joscthomas/jctsh/tos/Repo-Purposes.md

# Repo Purposes

**Author:** Joseph C Thomas (JCT), via Claude
**Purpose:** What each repo under `Projects/` is actually *for* — not the mechanical
description (that's `Projects/README.md`'s one-liner, and each repo's own `README.md`),
but the real benefit it serves and who it serves. Prompted by a sermon note (jctsh
`tos/kanban-board.md` CARD-0320): "It's not just about the system, it is about the
results, the benefits for people."
**Version:** 1.3
**Version description:** Added `Rethinking-Scripture-Bible-Study`'s section — a fourth
repo under `Projects/`, created after this doc's first three entries. From v1.3 onward,
writing this section is a standard step of `New-Repo-Setup-Protocol.md` (step 9) for any
future repo, not something done after the fact.

---

**Template each entry follows:** Primary beneficiary → Origin → Core value/satisfaction
→ Secondary beneficiaries (if any) → Emergent/secondary purpose (if one exists — not
forced) → Open question / where this is heading (if genuinely unresolved).

## jctsh

- **Primary beneficiary:** Joseph.
- **Origin:** a decade of general tech interest (a SmartThings hub, basic household
  sensors), accelerating sharply in the last year into hands-on ESP32 firmware, circuit
  design, and 3D printing — a lifelong pull toward building tools and tinkering with
  electronics, from a career that started in programming before moving into
  project/program management.
- **Core value / satisfaction:** the puzzle itself — multi-dimensional, spanning
  hardware, firmware, and now AI-assisted development — and the specific pleasure of
  problem-solving through to something that actually works. A distinct, especially
  strong thread: Joseph hikes several times a week, and building gadgets to bring on
  those hikes (`hiking-monitor`, `air-quality-monitor`, `hike-izer`) is not incidental
  to the rest of the hobby — it's one of its clearest expressions.
- **Secondary beneficiary:** Robin — benefits from specific features, not all of it,
  and is generally supportive of the time Joseph spends on it.
- **Emergent/secondary purpose:** writing ESP32 firmware became the on-ramp to
  understanding AI-assisted development, initially by accident and now deliberately —
  using AI/Claude Code to build out a personal "operating system" (echoing jctsh's own
  `tos/` naming) is now an explicit, exciting direction in its own right, not just a
  side effect of the hobby.
- **Note on "critical":** not everything here is load-bearing (the garage door
  automation isn't essential infrastructure), but several things have become
  genuinely, daily-enjoyed conveniences regardless — the line between "hobby project"
  and "thing we actually rely on and like using" isn't as clean as it might sound.

## LogSeq

- **Primary beneficiary:** Joseph.
- **Origin:** a long-standing want to keep track of notes for a variety of purposes,
  after trying different note-taking tools over the years. LogSeq's specific model —
  daily journals, tagging, plain markdown files — is what's actually worked.
- **Core value / satisfaction:** central to Joseph's life, and reflected heavily in
  what gets captured here, is an ongoing pursuit — as a follower of Jesus, developing a
  real relationship with God and learning to love God and people, worked at for a long
  time, not a phase or a project with an end state. Notes along these lines (sermon
  notes, devotionals, scripture reflection) resonate with that quest and are a natural,
  central use of the tool.
- **Also tracked here, not secondary in importance, just distinct:** other things that
  matter to Joseph — ideas, ordinary life notes, now music — alongside the above, not
  subordinate to it.
- **Open question, not yet resolved:** how to actually *leverage* what accumulates here
  — not just capture and file it away, but do something more with it. Working with this
  repo and its tools (a Claude Code session operating directly in it, as this session
  has) may turn out to be part of how that gets figured out.

## PB-Blog

*Blog by Pastor Ben Walls, Sr. (pastorbenwalls.com). "Rethinking Scripture" is a separate repo (the new Bible study content, CARD-0317) — not this blog's title; corrected 2026-09-20 after conflating the two.*

- **Beneficiaries:** blog readers, Pastor Ben, and Joseph himself — serving these
  constituents while also learning through the editor role.
- **Origin:** ~20 years serving as editor for Pastor Ben's devotional blog — learned
  WordPress and the craft of editing/publishing itself first.
- **Core value / satisfaction:** started as learning the craft of editing and
  publishing; has grown into learning and using an increasingly augmented toolset
  (Grammarly, and now Claude-assisted editing/formatting automation) — a genuine
  learning bonus, echoing jctsh's AI-learning thread but in a different register: here
  it's a welcome side benefit of the editorial work, not (yet) a deliberate central
  direction the way it's become in jctsh.
- **Real risk this repo addresses — not platform risk, key-person risk:** the concern
  isn't WordPress disappearing, it's the risk of losing the person (Joseph) who's been
  driving this for so many years. A clean, technology-independent representation of the
  material — a real source of truth, per PB-Blog's own `kanban-board.md` CARD-0003 —
  would outlast any one person's continued involvement, not just any one platform.
- **Emergent purpose:** persisting Pastor Ben's legacy — a genuine service to him, with
  benefit extending to his family. Possible futures this could enable: a searchable
  archive, or Pastor Ben or his family compiling a book from the material. Who else
  might find it valuable isn't known, and that's fine — left open rather than forced.

## Rethinking-Scripture-Bible-Study

- **Beneficiaries:** any Casas Church small group whose members have gone through
  Pastor Glenn's "how to read the Bible" class — currently, Joseph's own small group,
  beta-testing the material. Eventually intended for the small-group ministry and the
  church more broadly.
- **Origin:** Joseph's own participation in Casas Church leadership training, going
  through Glenn's class multiple times, developed in partnership with the church's
  small group ministry.
- **Core value / how it works:** reinforces Glenn's class material through group
  discussion — the study alone isn't sufficient to convey what the class covers, so
  this exists to extend it. Not top-down teaching: each session's host facilitates
  rather than teaches, and the actual value is in the discussion and interaction among
  group members, not content delivery.
- **Emergent/deeper purpose:** in service of Pastor Glenn's broader goal — changing the
  church's culture around how people read and interpret the Bible. This material is one
  instrument toward that larger cultural shift, not an end in itself.
- **What this repo's toolset is actually for:** iterating on the material based on real
  beta-test feedback — mostly informal notes from small-group discussion sessions, some
  written notes from facilitators. Joseph believes this Claude Code toolset can help
  process that feedback into the next improved version.
- **Open question, not fully resolved:** ownership trajectory — expected to eventually
  become official small-group-ministry material under the church's own ownership,
  though Joseph may stay involved supporting it.

---

**Related:** `Projects/README.md` (the one-line-per-repo quick-orient surface this
deepens, not replaces), `tos/kanban-board.md` CARD-0320 (the card this doc fulfills),
`tos/Protocol-Placement.md` (the shared-but-not-universal placement precedent this
follows), `tos/New-Repo-Setup-Protocol.md` (step 9 — writing a new repo's purpose
section here is now a standard part of setting one up).
