joscthomas/jctsh/core/data-pipeline/RUNBOOK-sheets-outage.md

# Runbook -- the environmental Google Sheet stops accepting writes

> **RETIRED 2026-09-29 (CARD-0349, CARD-0366).** The environmental data no longer lives in a Google Sheet, so none of the Sheet-specific triage below applies. Kept for its incident history (CARD-0226) and because the Node-RED queue/replay behavior in section 0 still holds. For the current system's health, backup and restore, see `README.md`.

Written 2026-09-25 after the CARD-0226 incident. Symptoms: node-red Alerts such as
`Environmental Data POSTs failing (...)`, gaps in the porch/patio/hiking-monitor rows,
hike pages built with no environmental data, Apps Script Executions showing `Timed Out`
(360 s) or `Failed` (~93 s / ~187 s).

**You will normally hear about it first from the Sheet Health probe** (Node-RED tab "Sheet Health", CARD-0338):
a push to the Pixel and a log line from component `sheet-health` after two consecutive bad or >10 s checks
(~10 minutes worst case), a repeat every 30 minutes while it stays bad, and a `recovered after N min` line.
To exercise it: click the `TEST: force next 2 probes to fail` inject in that tab, then `every 5 min` twice, then once more.
The unattended daily refresh and backstop on the M8 skip themselves while the Sheet is unhealthy (a skipped daily
refresh must be re-run by hand: `docker exec hike-izer-orchestrator python3 generation.py --daily-refresh`).

## 0. Nothing is being lost -- don't rush

- **Node-RED holds readings** (serial queue, one POST in flight, retries every 5 min, alerts at
  most once per 30 min, discards a reading only after 24 h). The queue is **in memory**:
  a redeploy of the Environmental Data tab, or a Node-RED restart, empties it (see section 5).
- The phone apps (GPSLogger, Tasker observations) queue their own posts and retry.
- hiking-monitor and the AQM keep their logs on the device until the *next* run starts
  (CARD-0226), and can re-send them (hiking-monitor: "Replay Hike Log" button in HA; AQM:
  publish anything to `jctsh/components/air-quality-monitor/command/replay` while connected).
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
