joscthomas/jctsh/core/data-pipeline/timescaledb-migration-plan.md

# Migrating the Environmental Data pipeline off Google Sheets to TimescaleDB

**Tracking card:** CARD-0349. **Status:** Planning. Decided so far (Joseph, 2026-09-27): technology is
TimescaleDB; it runs on the M8; Google Sheets is retired once migration is verified, not kept as a
synced mirror; the HTTP API in front of it is redesigned as part of this, not preserved as-is.
Scope covers all 5 sheets, built in two phases — Phase 1 (Environmental Data + GPS Track) first,
Phase 2 (Hiking Observations, Wildlife Detections, Hike Start Forecast) once Phase 1 is proven live.

This document is the planning artifact CARD-0349's own Planning → Design trigger needs
(`JCTsh-Operating-System.md`). It is not final SQL/code — Design/Build fills in exact statements —
but it's specific enough that Design shouldn't need to re-derive the schema or consumer list from
scratch.

---
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
