joscthomas/jctsh/tos/JCTsh-Component-Session-Start.md

# Component/Cluster Session Start

**Author:** Joseph C Thomas (JCT), via Claude
**Purpose:** The startup steps a persistent component or cluster session (CARD-0284) actually runs instead of the general Session Start (`tos/JCTsh-Session-Start.md`) — some general steps scoped down, some skipped, some run unscoped, plus component-only steps with no general-session equivalent.
**Version:** 1.23
**Version description:** `JCTsh-Session-Start.md` gained a new general-session step 9 (credential rotation check, CARD-0372's `secret.ps1 due`), pushing its old step 9 (`/status`) to step 10 -- this document's own step-mapping table and its "per step 9" cross-reference updated to match, and the new step added as row 9, Skipped (the registry has no per-component tag to scope by yet).
**Version history:** `JCTsh-Component-Session-Start-History.md`

---

A **component session** — which includes a **cluster session** (CARD-0284: a group of related components with one shared session, e.g. "the hike-izer session" covering `hike-izer`/`hike-izer-orchestrator`/`hike-izer-web`/`core/data-pipeline`) — is a session with a standing, resumed identity dedicated to one or more specific components. This is distinct from a general session with no such persistent focus (yet) established.

## Initiating or Rebuilding a Component Session

Three real instances exist as of 2026-09-18 — see the Session Roster below for the current list — generalized here into a repeatable procedure for starting a new one, or reconstructing an existing one that's been lost or never formally initiated:

1. **Decide the scope.** One component, or a cluster of related components that findings routinely travel across together (CARD-0284's cluster-level granularity guidance) — not one session per individual file or feature.
2. **Give it a plain name using `/rename`** (e.g. "the hike-izer session," "the tos session") — not cosmetic: this is the actual mechanism `/resume`/`claude --resume` use to find and reopen a specific session by name later, confirmed directly against Claude Code's own docs (2026-09-21), not assumed from the command's surface behavior. **Revised 2026-09-18 (CARD-0299) — a registry now exists,** reversing this section's original "no separate registry or naming file is needed" line: that call was right at two organic instances with no drift risk yet, but a third (deliberately initiated, not organic) showed real value in having a real roster to check against, not just prose naming two examples. See the Session Roster section below.
3. **Run the startup steps below** (this document's per-step table plus its three component-only read steps, scoped to the chosen component(s)) — this is the entire initiation procedure. There is no separate "setup" step beyond actually running startup scoped to the new component(s) for the first time. **Reconcile against the Session Roster (CARD-0299) as part of this step:** if this session's name already has a roster entry, confirm its covered components still match — a genuine drift (a component added or dropped since) gets fixed by updating the table to the session's actual current scope, not silently ignored. If no entry exists yet (a genuinely new session), add one. If the session's *intended* scope doesn't match what an existing same-named entry says, that's a real conflict to resolve explicitly — decide whether the session's own scope should change to match the table, or the table should change to match the session — never silently pick one without noting why.
4. **From then on, default to resuming it** (CARD-0284's workflow) — the session's own history is a speed cache, not the source of truth, so nothing is lost if it's later abandoned and needs rebuilding: re-running the same startup steps against the same component(s) reconstructs full working context from the `.md` files alone, per CARD-0284's original "cache layer, not a second store" design. This is what makes "rebuilding" identical to "initiating" — there's no separate recovery procedure to maintain. Mechanically, resuming doesn't require staying inside an existing session: from a clean shell/terminal, `claude --resume` (pick it from the list) or `claude --continue` (if it's the most recent) reaches the same session just as well as `/resume` from within another one — the practical way to run two component sessions side by side is simply two terminal windows, each resumed independently.

**`/clear` is a different case from the rebuild above — same process, wiped conversation, not covered by the "resume from a clean terminal" language (added 2026-09-21).** `/clear` starts a fresh conversation inside the *same* running process, and a name set via `/rename` genuinely survives it — the new post-clear conversation keeps the name, and the old pre-clear one stays separately resumable under it too. But the name is only a label. Everything the session had actually read and internalized — the component's `README.md`/`CLAUDE.md`, its scoped card context — is gone with the conversation. A `/clear`'d component session is still *findable* by name, but it is not still *scoped*: whoever resumes it needs to explicitly re-run this document's startup steps again, the same as any other rebuild, rather than assuming the surviving name means the surviving context.

**No technical enforcement of scope, at all — this whole scheme is discipline, not a restriction (added 2026-09-21, in response to Joseph asking directly how effective this actually is).** Naming and the Registry make a session's *intended* scope discoverable and its drift *checkable* at initiation time. Neither one — nor anything else in this document — stops a named, scoped session from reading or editing files outside its stated scope mid-conversation, and nothing re-checks that boundary continuously once a session is running. The only backstop is the Registry reconciliation in step 3, which only runs when a session is (re-)initiated, and the same "any card-related request defaults to this session's own component tag(s)" convention below, which depends on the model actually following it. Worth knowing as a real limit of this design, not assuming it's airtight because it's written down.

## Component/Cluster Registry

Added 2026-09-18 (CARD-0299, refined same day — Joseph: "this table identifies the clusters"). **This table's primary job is identifying which clusters exist** — which named groupings of components have been decided as a unit — not just which ones happen to have a running session. A cluster can be identified here before anyone starts a session for it (the **Initiated** column below is exactly for that case); once initiated, the same row also tells you it's resumable. Kept current by the reconciliation check in step 3 above, not by a separate audit mechanism. **Purely a roster of clusters and their sessions** — name and covered components only. It does not track kanban tag ownership; that's `kanban-board.md` CARD-0294's separate concern (a directory/tag reconciliation), and the two are deliberately kept from restating each other.

| Cluster | Covered components | Initiated | Status |
|---|---|---|---|
| architecture | `architecture` | No | — |
| equip-shelf | `equip-shelf` | No | — |
| garage cluster | `automatic-garage-door-opener-closer`, `garage-presence`, `garage-radar`, `salt-sensor` | Yes | Active |
| HA automations cluster | `outdoor-presence-detection`, `traveling`, `core/homeassistant` | No | — |
| hike-izer | `hike-izer`, `hike-izer-orchestrator`, `hike-izer-web`, `core/data-pipeline` | Yes | Active |
| hiking-monitor cluster | `hiking-monitor`, `air-quality-monitor` | Yes | Active |
| jctsh-menu | `jctsh-menu` | No | — |
| LogSeq | `LogSeq` (whole separate repo, not a jctsh-internal directory) | Yes | Active |
| network/infra-visibility cluster | `netalertx`, `core/mqtt`, `core/logging`, `core/node-red` | Yes | Active |
| ops cluster | `core/maintenance`, `core/docker`, `hosts/m8`, `hosts/pi1` | Yes | Active |
| outdoor/backyard cluster | `remote-temp-sensor-01`, `weather-station` | Yes | Active |
| PB-Blog | `PB-Blog` (whole separate repo, not a jctsh-internal directory) | No | — |
| photo-server cluster | `photo-server`, `photo-quality-review`, `photo-tv-display` | Yes | Active |
| porch/patio temp sensors | `front-porch-temp-sensor`, `back-patio-temp-sensor` | Yes | Active |
| Rethinking Scripture Bible Study | `Rethinking-Scripture-Bible-Study` (whole separate repo, not a jctsh-internal directory) | No | — |
| tos | `tos` | Yes | Active |
| van cluster | `p-w-firefly`, `van-sensors`, `bedside-clock` | No | — |

**Predefined clusters, added 2026-09-18 (Joseph: "add all the clusters... so they are predefined") — every component/core/host directory now has a home, none of them started yet.** Groupings are judgment calls based on real evidence of components' findings traveling together, same discipline as the three already-initiated clusters, not arbitrary:
- **hiking-monitor cluster** — Session Card Selection's own top recommendation (CARD-0284's closing note): highest cross-work volume of any ungrouped component (41+4 tagged cards), and real shared history (the field-device three-signal framework in `JCTsh-Build-Standards.md` §2.14, the debug-UART investigation, battery/regulator-headroom physics hit both the same night). **Actually initiated 2026-09-20** — not via the clean "open a new terminal" procedure above, but by Joseph directly asking an already-running hike-izer session to re-scope itself mid-conversation, to pick up CARD-0259's Planning work. A real, if messier, instance of the same startup steps (git status/Build column/recent activity/markers re-run scoped to `hiking-monitor`+`air-quality-monitor`, both components' README.md/CLAUDE.md read in full) rather than a fresh terminal — the procedure above doesn't yet describe this in-place re-scoping path explicitly.
- **garage cluster** — already documented as one system in `auto-garage-door-system.md`, referenced by both `automatic-garage-door-opener-closer/CLAUDE.md` and `garage-presence/CLAUDE.md`. **`salt-sensor` added 2026-09-25 (Joseph)** — moved in from its former single-component row; rationale not yet written up, corrigible like any other grouping here.
- **HA automations cluster** — pure HA-native automation components (no dedicated hardware), sharing `automations.yaml` and the same HA infrastructure.
- **network/infra-visibility cluster** — the "watch everything" layer: dashboard, broker, flows, network scanning.
- **ops cluster** — scheduled-job/host-management layer (reboots, backups, update checks) — distinct from `tos` itself, which owns the kanban/process system rather than physical host operations.
- **outdoor/backyard cluster** — all still Planning-stage, but `JCTsh-Build-Standards.md`'s power-architecture standards (§2.14) were written with exactly this class of device in mind; grouping means the pattern gets applied consistently from the start rather than independently rediscovered. **Initiated 2026-09-22** — startup steps ran scoped to the four components originally grouped here; none had a `README.md`/`CLAUDE.md` yet (all still pre-Build, no directory had produced that split), so the component-only read steps covered each one's own planning doc(s) instead. **Narrowed same day** — `van-sensors`/`bedside-clock` moved out into the new `van cluster` row (Joseph's table rearrangement); current membership is whatever the table above shows, not restated here so this bullet can't drift out of sync with it again.
- **~~salt-sensor,~~ jctsh-menu, ~~front-porch-temp-sensor,~~ ~~p-w-firefly,~~ equip-shelf** — each self-contained enough (no real recurring cross-work found with anything else) that forcing a grouping would be arbitrary; single-component clusters, not omissions. **`front-porch-temp-sensor` struck 2026-09-21** — no longer self-contained once `back-patio-temp-sensor` was built as a direct clone of it; see the porch/patio bullet below. **`p-w-firefly` struck 2026-09-22** — moved into the new `van cluster` row below (Joseph's table rearrangement). **`salt-sensor` struck 2026-09-25** — moved into the `garage cluster` row (Joseph).
- **van cluster** — added 2026-09-22 (Joseph, table rearrangement): groups `p-w-firefly` with `van-sensors`/`bedside-clock`, all van-related per the cluster's own name. Not yet interviewed for a fuller rationale the way the other groupings above are — corrigible like any other row here, per the closing line below.
- **porch/patio temp sensors cluster** — added 2026-09-21 (Joseph, at this cluster's own initiation), merging what had been a single-component `front-porch-temp-sensor` row with the newly-directoried `back-patio-temp-sensor`. The strongest "findings travel together" evidence of any grouping here, and not a judgment call the way the 2026-09-18 proposed groupings were: CARD-0219 defines back-patio explicitly as a duplicate of front-porch's design — same ESP32 DevKitC-32 / BME280 / BH1750 hardware, same I2C pin assignment, same ESPHome firmware pattern, same MQTT/Node-RED/Sheets path — so a wiring, flashing, or integration finding on either one applies to the other by construction, not by coincidence. The two differ only in location (points H8 vs. P2 in `house-lot-coordinates.md`) and in whether custom HA threshold automations exist yet (front-porch has two; back-patio's are deliberately deferred, `integration.md`).
- **`core/offline-logger`** deliberately has no row — a reusable template (`sensor_logger.h`) copied into whichever sensor uses it, not a component with its own ongoing thread; it belongs to whichever cluster actually uses it at the time.
- **architecture** — added 2026-09-18 (CARD-0294's tag reconciliation, once retagging `[infrastructure]` cards revealed a genuine residual bucket that needed a real directory): doc-only, not a component or host, same shape as `tos`'s own row — a single-"component" cluster where the covered "component" is the directory itself.
- **LogSeq, PB-Blog, Rethinking Scripture Bible Study** — added 2026-09-20 (CARD-0315's third interim call, from a LogSeq-scoped session asking to run this document's startup), each a whole separate sibling repo under `Projects/`, not a jctsh-internal `components/`/`core/`/`hosts/` directory — same single-"component" shape as `tos`'s and `architecture`'s rows, just one level up (the repo itself is the "component"). **A real mismatch this extension doesn't paper over:** the 9-step table below (steps 1/2/3/5/6/9) was written assuming jctsh's own shared `kanban-board.md`/git tree — scoped to one of these three, those steps point at *that repo's own* `kanban-board.md`/git tree instead, which (at least for LogSeq/PB-Blog) uses a different one-bracket card format with no jctsh-style component tags to scope by (CARD-0313's finding), and steps 4/8 (jctsh's auto-PR intake, `archive_cards.py`) don't apply at all — no such pipeline/script exists in those repos. CARD-0315 stays open on the bigger question this is one instance of.
Not yet checked against Joseph's own judgment — these are proposed groupings, corrigible like any other card content, not a final decision just because they're written down.

**Reconciled against `kanban-board.md`'s actual tags, 2026-09-18 (CARD-0294's own closing step).** Every non-type tag currently in use that names a real `components/<name>/`, `core/<name>/`, or `hosts/<name>/` directory resolves to exactly one row above — no orphaned directory tag, and no directory claimed by two clusters. Three things this check deliberately did *not* try to reconcile, because they aren't directory tags at all: (1) tags for **planned components with no directory yet** (`vu-meter`, `shower-temp-sensor`, ~~`back-patio-temp-sensor`,~~ `garage-entry-hallway`, `presence`, `wildlife`) — correctly absent here, since this table tracks real components, not ideas; they'll get a row (new or joining an existing cluster) once actually built, per the same iterative/incremental discipline as everything else in this doc. **`back-patio-temp-sensor` struck 2026-09-21** — it now has a real directory and a real row (the porch/patio temp sensors cluster above), so it is no longer an example of this case. Worth keeping visible rather than deleting, because it is also the one real exception to the "directory appears when the build starts" assumption this bullet rests on: `JCTsh-Component-Planning-Pattern.md`'s "Cloning an Existing Component" section creates the directory at *Planning*, not Build, so a clone-shaped card can legitimately outgrow this list before reaching Build (already noted on CARD-0294 in `kanban-board.md`; recorded here too so the list itself carries its own exception); (2) `personal` — non-project life-admin cards (DNS records, digital-identity checklists), not a component tag and never meant to have a cluster; (3) **multi-directory clusters use per-directory tags, not one unified cluster tag** — e.g. the ops cluster's four cards use `[m8]`/`[pi1]`/`[maintenance]`/`[docker]` individually, never `[ops]`, because `archive_cards.py` (CARD-0294) routes on the literal directory name. A cluster groups tags for session-scoping purposes; it doesn't rename or merge them.

**One component, one owning cluster — never listed under two (decided 2026-09-18, Joseph asking directly about `air-quality-monitor`'s real dual relevance).** `air-quality-monitor`'s firmware/hardware work belongs with `hiking-monitor` (shared power architecture, shared debug-UART investigation); its *data* also flows through hike-izer's pipeline (CARD-0285). That doesn't make it dual-membership — it stays solely under `hiking-monitor cluster`. A session whose work needs another domain's info reads that domain's files directly (`README.md`/`CLAUDE.md`, CARD-0284's own workflow) without needing to *own* it. Listing a component under two clusters would create real ambiguity — which session's startup actually reads its docs, and whose `CLAUDE.md` edits are the curated truth if both write to it — the same single-source-of-truth principle `JCTsh-Operating-System.md` already applies to documentation, applied here to component ownership instead.

**Cluster** names the grouping; once initiated, the actual `/resume`-findable session name follows step 2's convention — "the `<cluster>` session" (e.g. cluster `hike-izer` → "the hike-izer session").

**Initiated** (added same pass, Joseph) — whether this row is a real, running session reachable via `claude --resume`/`/resume`, or just a recorded scope not yet started. A "No" row is a candidate/recommended cluster (e.g. a Session Card Selection-style suggestion worth naming before anyone acts on it) — it exists on the registry so the scope is decided and discoverable, but there's nothing to resume yet. Once actually initiated per the procedure above, flip to "Yes."

**Status** is a manual designation, not automatically detected — "Active" means the session is in current use; a cluster deliberately retired or merged into another would be marked "Dormant" with a note, not silently dropped from the table (same "kept as a stub, not deleted" discipline as a retracted card). Only meaningful once **Initiated** is "Yes" — a not-yet-started candidate has no Active/Dormant state to speak of.

---

**A periodic deliberate restart is a real, worthwhile exception to "always resume," not just a fallback for a lost session (added 2026-09-17).** Three genuine benefits, weighed against the ramp-up cost this whole design exists to avoid: (1) **context/cost bloat** — a long-lived session's transcript keeps growing every turn, so a fresh one costs less per turn even with auto-summarization; (2) **self-testing the "cache, not source of truth" claim** — a session that's never rebuilt never actually proves the `.md` files are sufficient on their own, and a rebuild is exactly the mechanism that surfaced two real documentation gaps in this same `tos` session (CARD-0290's incomplete migration, the whole-board-vs-scoped listing miss); (3) **sheds stale intermediate reasoning** — corrected mistakes and abandoned approaches linger in a long session's context even after the docs are fixed, while a rebuild starts from only what's currently true. Not scoped to a specific cadence yet — periodic, judgment-based, the same "don't over-engineer before a real need shows up" discipline as the rest of this practice.

**A component session does not run `CLAUDE.md`'s general Session Start steps unmodified (corrected 2026-09-17, Joseph — this document previously said it did).** Each of the 9 general steps is either scoped to this session's own component(s), run exactly as a general session would, or skipped outright — never blindly run whole-board on top of everything below. This table replaces the general list for a component session; it isn't additional to it:

| # | General Session Start step | Component session treatment |
|---|---|---|
| 1 | `git status --short` for uncommitted changes | **Scoped** — check status only for files under this session's own covered component director(y/ies), not the whole repo. |
| 2 | `kanban-board.md` Build column | **Scoped** to this session's own component tag(s), not the whole board. |
| 3 | `kanban-board.md` cards updated in the last 7 days | **Scoped** to this session's own component tag(s), not the whole board. |
| 4 | Open GitHub PRs (auto-intake pipeline) | **Skipped** — a raw finding's component often isn't identifiable until reviewed; triaging the whole intake queue isn't this session's job. |
| 5 | Auto verify markers (date-based) | **Scoped** to this session's own component tag(s). |
| 6 | Watch for markers (event-based) | **Scoped** to this session's own component tag(s). |
| 7 | Read `tos/JCTsh-Operating-System.md` | **Unscoped** — runs in full, exactly like a general session. Foundational process knowledge (columns, triggers, Engineering Discipline), not a per-component data scan. |
| 8 | Periodic `archive_cards.py` dry-run check | **Skipped** — whole-board file-size housekeeping, unrelated to any specific component. |
| 9 | Credential rotation check (`secret.ps1 due`, CARD-0372) | **Skipped** — `tos/credential-registry.yaml` has no per-component tag to scope by today (holders name a component in free text, not a structured field), so this stays a general-session-only check until that's real. Revisit if the registry ever supports filtering by component — don't build that scoping ability speculatively before it's needed. |
| 10 | `/status` device-health check (CARD-0282) | **Scoped** to this session's own covered component(s)/device(s), not the whole fleet. The freshness/connection part needs no credential — `/status.json` (CARD-0330) — the fuller Alert/log scan (`/data`, structured JSON) uses `DASHBOARD_PASS` relayed from the vault (`secret.ps1 run -Name log-dashboard-password`, CARD-0372, 2026-10-03 — ask Joseph directly only if that entry isn't seeded or the call fails), per `JCTsh-Session-Start.md`'s own step 10. |

**Any card-related request made mid-session, not just the automated steps above, defaults to this session's own component tag(s)** unless Joseph asks for the whole board explicitly (Real miss, 2026-09-17: a "list the open cards" request during the `tos` component session was answered against the whole board instead, because the prior wording only covered the automatic startup sweep, not requests made later in the session). Same default applies to the `/status` check (row 10) for any ad hoc device-health question asked mid-session.

Then, additionally — steps with no general-session equivalent at all, specific to a component session:

1. **Read each covered component's `README.md` in full.** Per `JCTsh-Build-Standards.md` §7.1, `README.md` is the permanent reference — hardware, wiring, known behaviors, current capabilities/limitations — while `CLAUDE.md` is history and design rationale. Read once per resume, not just skimmed for whatever the immediate task is, so a hardware-capability question that comes up mid-session doesn't need rediscovery from scratch. (The real miss this step formalizes: CARD-0226/CARD-0222/CARD-0258, 2026-09-17 — five separate dated notes assumed hiking-monitor could run a debug-UART setup built for a different component, without ever checking hiking-monitor's own `README.md`/`wiring.md`, which would have shown it never had one.)
2. **Read each covered component's `CLAUDE.md` in full.** Current, curated context — design rationale, constraints, gotchas, open threads. As of CARD-0290 this stays genuinely small (archived card history now lives in a separate `card-archive.md` sibling, never appended directly into `CLAUDE.md`), so reading it in full at every resume is actually practical, not just aspirational.
3. **Read each covered component's own operating doc in full, wherever it actually lives — `.claude/skills/<name>/SKILL.md` above all (added 2026-09-22, after a real incident).** Steps 1 and 2 cover what a component *is* and why it's built that way; neither covers **how to operate it** — the runbook rules for actually invoking it, including which options cost real money or are opt-in-only. For anything with a Claude Code Skill, that's `.claude/skills/<name>/SKILL.md`, which is **not** under `components/<name>/` and so is missed entirely by steps 1–2 even for a session scoped to exactly that component. Also read any sibling runbook a covered component's `README.md` Files table points at as procedural rather than reference (e.g. `staging.md`, `*-pipeline.md`) **before running the pipeline it describes** — not on-demand afterward.
   **The real miss this step formalizes, 2026-09-22 (hike-izer cluster session):** a correctly-executed startup — general steps scoped, both `README.md`s and both `CLAUDE.md`s read — still never surfaced `.claude/skills/hike-izer/SKILL.md`'s explicit standing rule that `generation.py --step2`'s `--narrative` flag is opt-in-only and requires Joseph's explicit per-hike approval every single time (~$0.5–0.8/hike vs ~$0.06), with a generic "run step 2" named in that same rule as specifically **not** permission. Asked to "do the second pass for today's hike," the session reasoned its way to `--narrative` and had to be stopped mid-run by Joseph — who noted this was a repeat, not a first offense. Both component `README.md`s point at `SKILL.md`; this document didn't require opening it, so it wasn't opened.
   **The generalizable rule, not just the hike-izer instance:** a component's docs can carry standing operating constraints that are invisible from `README.md`/`CLAUDE.md` alone. Before *operating* a covered component (not merely reading or reasoning about it), confirm its operating doc has actually been read this session. When such a doc states a default for an ambiguous request, that default governs — resolving ambiguity toward the costlier or less reversible option is exactly the failure this step exists to prevent.

4. **Before compiling or flashing any covered ESPHome component, read `WORKSTATION-SETUP.md` in full and run `workstation-verify.ps1` (added 2026-09-28, CARD-0360).** This document's own general-session counterpart (`JCTsh-Session-Start.md`) already states this as a conditional, action-triggered step — but a component/cluster session runs this document instead of that one, so without a pointer here it was never actually reachable from a component session's own startup. Same shape of gap as step 3 above: `WORKSTATION-SETUP.md` is a workstation-level operating doc, not under any covered component's own directory, so steps 1–3 miss it even for a session scoped to exactly the ESPHome-flashed components it applies to (hiking-monitor cluster, garage cluster, porch/patio temp sensors cluster). Conditional on the action (about to flash/compile), not run at every resume the way steps 1–3 are.

**Not required — stays on-demand:** re-reading every detail doc a `README.md`'s Files table indexes (`wiring.md`, `power-system.md`, `ESP32-project-pins.md`, etc.) at every resume, and — explicitly, per CARD-0290 — each covered component's `card-archive.md`. Those stay read-when-actually-needed: detail docs per the Engineering Discipline rule (`JCTsh-Operating-System.md`) requiring a check before asserting a hardware-capability claim, `card-archive.md` only when a specific historical question actually needs it. Step 2 above is about `CLAUDE.md`'s own curated-context layer being fresh, not preloading every downstream/archival file every time.

**Related:** CARD-0284 (cluster-session origin and end-to-end workflow, closed Done once the photo-server cluster session proved the initiation procedure), CARD-0299 (this document's Session Roster and the reconciliation check in step 3), CARD-0294 (tag-to-directory reconciliation — a deliberately separate concern from the Session Roster), CARD-0292 (this document's own version-history split), `JCTsh-Component-Session-Start-History.md` (this document's full changelog), `JCTsh-Session-Card-Selection.md` (the analogous session-behavior document this mirrors in structure), `CLAUDE.md` (general Session Start — always runs first), `JCTsh-Build-Standards.md` §7.1 (README.md's role as permanent reference), `JCTsh-Operating-System.md` (Engineering Discipline section, Auto Verify / Watch For Markers section, Documentation Structure section — the card-archive.md filename standard), CARD-0290 (the CLAUDE.md/card-archive.md split this document was updated for).
