joscthomas/jctsh/components/back-patio-temp-sensor/parts-list.md

# Back Patio Temp Sensor — Parts List

Consolidated bill of materials for this build. Front-porch-temp-sensor's own BOM lived
in its Phase 4 instructions file (`front-porch-temp-sensor-claude-code-instructions.md`'s
Hardware Context table) — that file was deliberately skipped for this build (straight to
Build, per CARD-0219), so this file exists to hold the same consolidated view instead of
leaving it split with no single reference point. Per-step Materials sub-tables still exist
in `perfboard-layout.md` and `mounting.md` for at-a-glance use during those specific steps.

---
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
