joscthomas/jctsh/components/air-quality-monitor/perfboard_1.jpg

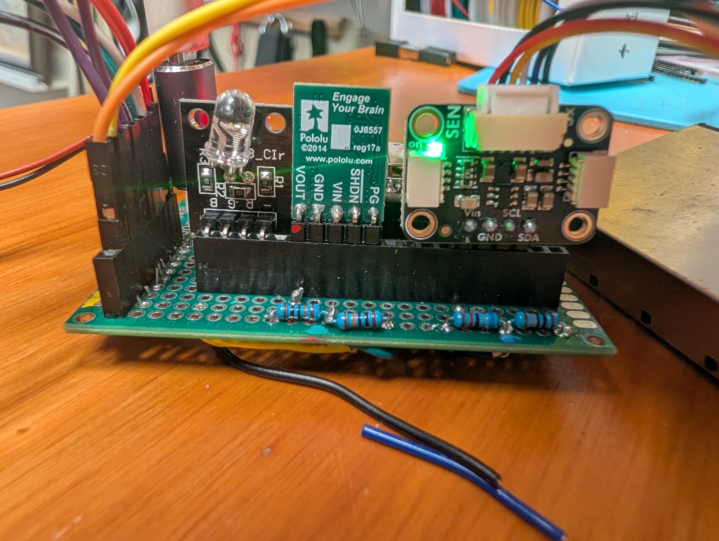
components/air-quality-monitor/perfboard_1.jpg
