joscthomas/jctsh/components/air-quality-monitor/perfboard_2.jpg

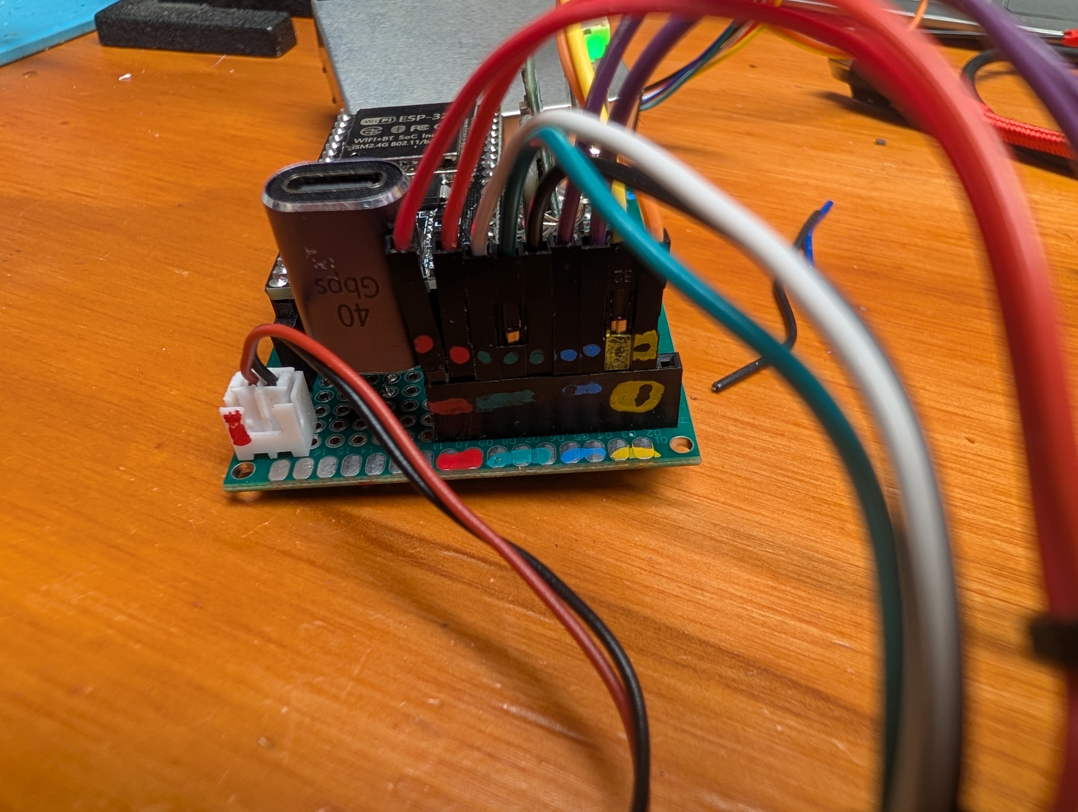
components/air-quality-monitor/perfboard_2.jpg
