joscthomas/jctsh/components/hiking-monitor/hiking_monitor_enclosure_3d.png

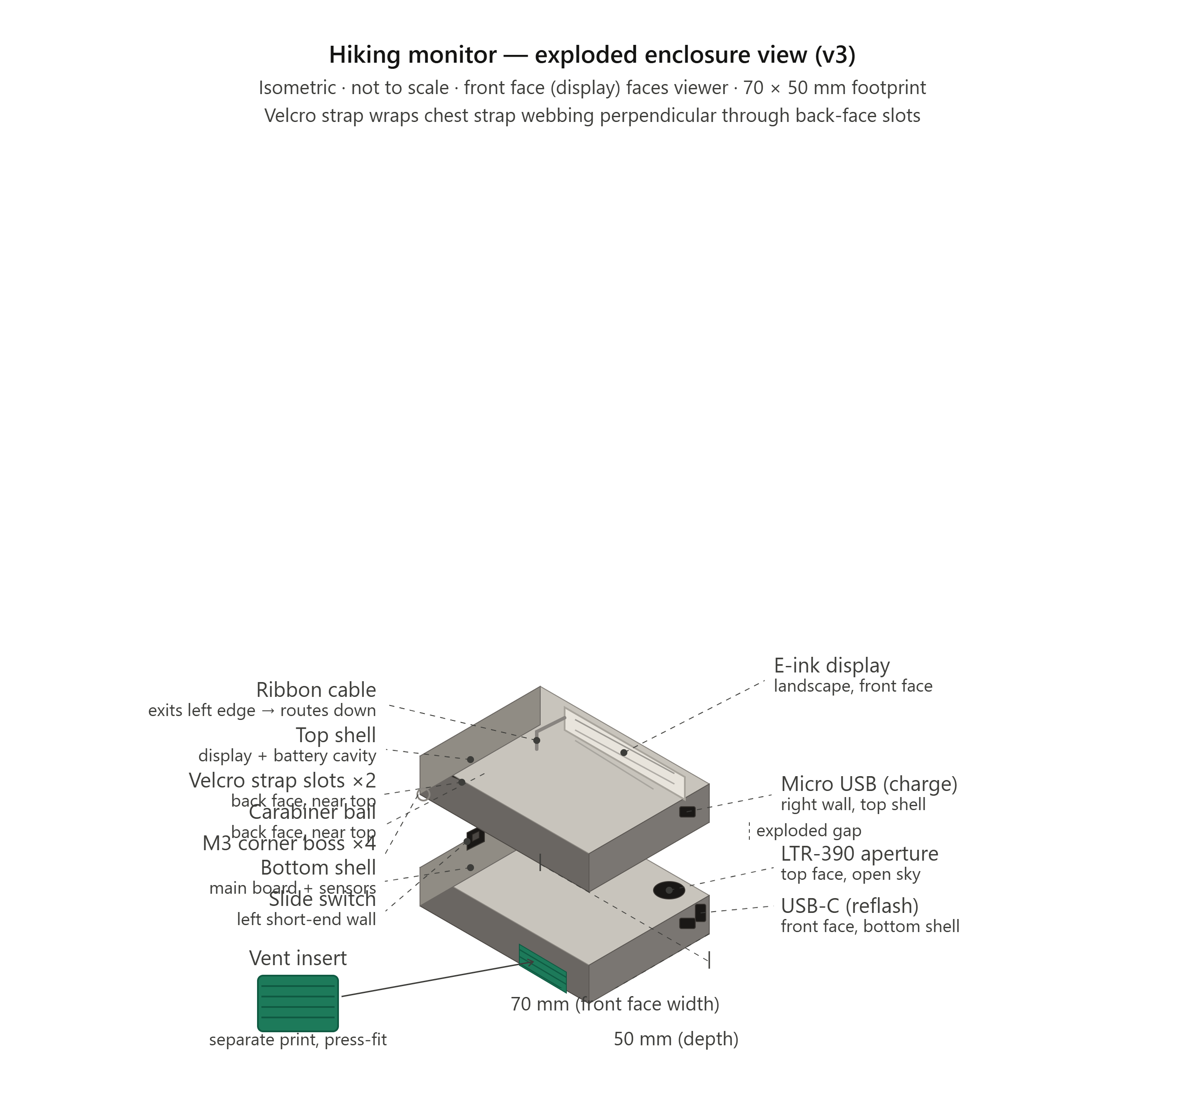
components/hiking-monitor/hiking_monitor_enclosure_3d.png
