joscthomas/jctsh/components/air-quality-monitor/air-quality-monitor-claude-code-instructions.md

# JCTsh Air Quality Monitor — Claude Code Instructions
**Author:** Joseph C Thomas (JCT)
**Purpose:** Step-by-step build instructions for `air-quality-monitor`, converting the decisions made in `JCTsh-air-quality-monitor-phase1.md` (Phases 1–3) into an executable build.
**Project:** JCT Smart Home (JCTsh)
**Version:** 1.3
**Version description:** Step 8's full design finalized 2026-09-09 (see Step 8 below): the boot-time WiFi-gate mechanism (including the priority-ordering finding that this device's `on_boot` — priority -100 — can safely call `wifi.disable()` directly, unlike hiking-monitor's priority-600 block, which had to defer to the interval), the bounded-attempt/retry state machine, SEN55's duty-cycle mode-switching timing (confirmed `SEN5X_CMD_START_MEASUREMENTS_RHT_ONLY = 0x0037` against the installed ESPHome source), the LED diagnostic scheme (Blue dedicated to networking status), and the MQTT logging plan (buffered vs. live per state) are all specified in full — ready to implement, not yet written to `air-quality-monitor.yaml`.
**Version 1.2 description (2026-08-19 to 2026-08-27):** Step 1 resolved (2026-08-19, Joseph): dock-detect-only for mode-switching confirmed, plus a new inline power switch (wired directly into the battery path, no GPIO) added for true transport/storage off — kept deliberately separate from mode-switching, per the CARD-0181 lesson that a GPIO-tapped switch only sets a mode flag rather than cutting power. Power architecture also changed from the originally-planned TP4056+boost combined module to a direct LiPo-to-LDO design (MCP1700) per `JCTsh-Build-Standards.md` §2.14 point 7 — recalculated runtime accordingly (see Hardware Context). **Revised 2026-08-27 (CARD-0218), resolving Step 8's Intent-signal gap:** this device now gets a real Intent switch after all — the existing Gebildet SS12D10 slide switch is repurposed from Power Switch duty onto GPIO27 (previously unused) as a GPIO-readable Intent signal, matching hiking-monitor's own pattern exactly; a new BK-1208 latching push button takes over the Power Switch role, inline in the battery+ path where the slide switch used to sit. See `JCTsh-Build-Standards.md` §2.14 point 12 for why these need to be two distinct physical controls, not one.
**Related files:** `JCTsh-air-quality-monitor-phase1.md`, `CLAUDE.md`, `JCTsh-Build-Standards.md`, `components/hiking-monitor/` (reference implementation — read before any firmware work, do not re-derive its patterns)

---

## Overview

`air-quality-monitor` is a portable, clip-mounted air quality sensor (PM1.0/2.5/4.0/10, VOC index, NOx index via a Sensirion SEN55) carried on hikes alongside hiking-monitor. Field-mode duty-cycle logging to onboard flash runs unconditionally, regardless of dock-detect state (**superseded 2026-08-20** — see Timeout policy below); dock-detect only triggers a background WiFi connection attempt (home or Pixel hotspot), and logging only pauses once that connection actually succeeds, at which point stored readings replay to MQTT. A single RGB LED gives real-time PM2.5 field awareness without a display.

This project inherits hiking-monitor's *firmware architecture* — it does not depend on hiking-monitor's physical enclosure, which remains a separate, unfinished, unrelated deliverable (CARD-0009).

---

## Working Pattern

Claude Code creates documentation and configuration files. Joseph follows those documents to perform physical assembly, wiring, flashing, and configuration work outside of Claude Code. Joseph reports results back, and Claude Code updates documentation to reflect actual findings, deviations, and lessons learned. Do not proceed to the next step until Joseph confirms the current step is complete.

---

## Hardware Context

| Component | Detail |
|---|---|
| Microcontroller | ESP32 DevKitC-32, 38-pin, CP2102 USB-C (Bag 1, 1 remaining after hiking-monitor) |
| Air quality sensor | Sensirion SEN55 (SparkFun SEN-23715 — corrected 2026-07-09, was mislabeled SEN54 in inventory). PM1.0/2.5/4.0/10, VOC index, NOx index. I2C address 0x69 (fixed). Integrated fan. ~59mm × 37mm × 23mm. |
| Adapter | Adafruit SEN54/SEN55 Adapter Breakout (#5964) — JST GH connector, onboard 5V boost (100mA), level shifting, STEMMA QT/0.1" I2C output. Lets 3.3V ESP32 logic drive the 5V SEN55 with no separate 5V supply. |
| ESPHome sensor driver | **Native `sen5x` platform** (esphome.io/components/sensor/sen5x/) — supports SEN50/54/55 directly over I2C. No custom component needed for the sensor itself. |
| Field indicator | RGB LED (Greekcreit kit, Plastic Box) — PM2.5 threshold color: green (<12 µg/m³), yellow (12–35), red (>35) |
| Power | EEMB LiPo pouch 603449 1100mAh (Bag 7) + TP4056 charging module (Bag 8, its boost stage unused) + MCP1700-3302E/TO LDO (Bag 32, on hand, same part validated on the CARD-0026/CARD-0070 rig) — direct LiPo-to-LDO architecture per `JCTsh-Build-Standards.md` §2.14 point 7, decided 2026-08-19 (**not** the boost-then-buck pattern originally planned in Phase 1 — see Power Budget note below for why this matters for real-world runtime). LDO `VIN` taps the battery+ node in parallel with TP4056's `BAT+` input, not fed from the boost module's output; LDO `VOUT` → ESP32 `3V3` pin directly. TP4056 continues managing charging/solar input unchanged — only its boost/`OUT+`/`OUT-` pads go unused. The Adafruit #5964 adapter's own onboard 5V boost (separate, self-contained, takes 3.3V logic in) is unaffected by this change — it never depended on the system-level boost module. |
| SEN55 power gate | **Dropped, 2026-08-21 (Step 6 decision).** SEN55 is hard-wired always-on (adapter `GND` directly to common ground — the Step 4 "bypass jumper" is now the permanent design, not a workaround) whenever the device itself has power. No BC547B/gate transistor, no GPIO27 involvement. Reasoning: Sensirion's own "Reduced Power Operation for SEN5x" doc recommends I2C mode-switching (Measurement ↔ RHT/Gas-Only) as the primary duty-cycle power-saving mechanism, not physically cutting power — and the inline power switch below already covers true full-off for storage/transport. That leaves no real use case for a dedicated gate, and eliminates the low-side-vs-high-side reliability question Step 4's diagnostic session surfaced (see CARD-0012 kanban notes for the full trail). Duty-cycling is now a Step 8 firmware task (I2C mode-switching), not a Step 6 hardware task. |
| Inline power switch | **Revised 2026-08-27 (CARD-0218) — role swapped from the slide switch to a new BK-1208 latching push button** (2-pin, DC 30V 1A, 12×8×8mm — same part chosen for hiking-monitor's CARD-0181; **ordered 2026-08-28**, one order covers both devices, not yet on hand/arrived). **Not a build blocker** — a spare SS12D10 (slide switch, Bin A3 assortment) stands in for this role on the breadboard until the BK-1208 arrives, same wiring/node, swapped in later with no other rewiring. Wired **directly into the battery+ path**, ahead of the TP4056/regulator, no GPIO involved — same position the original slide switch used to occupy. True hard off for transport/storage. Per `JCTsh-Build-Standards.md` §2.14 point 12: Power Switch and Intent need to be two genuinely distinct physical controls, not just electrically separate — the repurposed slide switch (below) is now Intent, so Power Switch needed its own, differently-feeling control rather than staying a second slide switch — the substitute slide switch here is a temporary stand-in, not a reversion of that decision. Pre-satisfies `JCTsh-Build-Standards.md` §1.7 before enclosure design even starts. |
| Intent switch | **New, 2026-08-27 (CARD-0218) — resolves Step 8's previously-open "no Intent signal" gap.** The existing Gebildet SS12D10 slide switch (SPDT, wired as SPST — Bag 23, on hand) is repurposed here, off battery-cutoff duty, wired instead as a plain GPIO-read digital input on **GPIO27** (previously unused, freed up when the SEN55 power-gate was dropped at Step 6) — same pin role and wiring pattern as hiking-monitor's own slide switch (GPIO27, internal pull-up, inverted logic). Answers "collecting field data, or idle/ready-to-upload" — the signal `dock_detect` was incorrectly standing in for until this decision. |
| Custom firmware component | Required for onboard flash logging + WiFi replay only (SEN55 reading itself uses the native platform above) — reuse `components/hiking-monitor/hiking_logger.h`, rename prefix per its own template instructions |
| Perfboard | Chanzon FR4, size TBD — measured in Step 3 below (SEN55 + adapter footprint is the dominant constraint) |
| Enclosure | **Deferred to a follow-on card** — clip case + carabiner, 3D-printed. **SEN55 mounts externally (decided 2026-08-20)**, 3M double-sided foam tape (on hand, Plastic Box) to the enclosure's smooth outer surface, cabled to the internal Adafruit #5964 adapter via the existing 100mm JST-GH cable through a small pass-through hole — no custom intake/exhaust venting needed, the SEN55's own sealed metal housing/fan shield handles its own airflow. See Future Enhancement section and `JCTsh-air-quality-monitor-phase1.md`'s Carry and Enclosure section. |

**GPIO assignments:**
| GPIO | Assignment |
|---|---|
| GPIO21 | I2C SDA (SEN55 via Adafruit adapter) — blue |
| GPIO22 | I2C SCL — yellow |
| GPIO34 | `battery_v` ADC — voltage divider midpoint (input-only pin, ADC1), 100kΩ/100kΩ divider, same pattern as hiking-monitor. **Corrected 2026-08-19** — this row previously said 68kΩ/68kΩ, but hiking-monitor's actual `wiring.md` uses 100kΩ/100kΩ for its battery divider; 68kΩ/100kΩ is the *dock-detect* divider, a different one (see the GPIO32 row below, unaffected). |
| GPIO32 | Dock-detect divider — same 68kΩ/100kΩ pattern and pin as hiking-monitor's `IN+` divider (USB present → HIGH, absent → LOW) |
| GPIO27 | **Intent switch** (added 2026-08-27, CARD-0218) — the repurposed slide switch, same pin/pattern as hiking-monitor's own Intent switch. Previously reserved for the SEN55 power-gate transistor base, dropped 2026-08-21 (see Hardware Context table above), then briefly unused until this assignment. |
| GPIO18 | RGB LED — Red |
| GPIO19 | RGB LED — Green |
| GPIO23 | RGB LED — Blue |

**Step 1 — resolved 2026-08-19 (Joseph), revised 2026-08-27 (CARD-0218):** dock-detect-only for firmware mode-switching is **no longer the design** — superseded once the three-signal gap was found (see the Step 8 note below for the full story). Current design: a real GPIO-readable Intent switch (the repurposed slide switch, GPIO27) plus a separate inline Power Switch (the new BK-1208 push button, no GPIO) — see the Hardware Context table above for both. This still keeps the same two concerns (which firmware mode vs. is the device powered) deliberately separate, per the original CARD-0181 lesson — it just now uses a real switch for the first one instead of `dock_detect`, which was never a valid stand-in for it.

**I2C addressing:** SEN55 only (0x69, fixed) — no other I2C devices on this bus, no conflicts, no bus-sharing concerns.

**Power budget — recalculated for the LDO swap, 2026-08-19:** `JCTsh-air-quality-monitor-phase1.md`'s existing estimate (~13-15mA average → ~58-68 hours) totals SEN55 duty-cycled draw + SEN55 idle + ESP32 light-sleep average, but — same blind spot CARD-0026 found on hiking-monitor — never included the boost module's *own* quiescent current. Hiking-monitor's real measured figure for that combined TP4056+boost module was ~22.6mA, continuous, regardless of sleep state. Had this build kept the originally-planned boost module, real-world runtime would likely have landed closer to 1100mAh ÷ (~14mA + ~22.6mA) ≈ **~30 hours** — notably worse than the Phase 1 doc's stated 58-68h, not because the consumer-side estimate was wrong, but because the regulator's own overhead was never in the total.

With the LDO swap (MCP1700's own quiescent draw is ~1.6µA — negligible), that hidden overhead goes away entirely. Runtime should land close to what the original consumer-side budget alone implies: 1100mAh ÷ ~13-15mA ≈ **~73-85 hours (roughly 3-3.5 days)** of continuous field-mode operation — comfortably beyond any realistic hike duration, and a real, concrete benefit of the LDO decision beyond just matching the standing §2.14 point 7 recommendation. Treat both figures as estimates pending Step 6's actual bench-measured current draw, same as hiking-monitor's own numbers were corrected from calculated to measured.

---

## Network / Integration Architecture

```
SEN55 (I2C 0x69, via Adafruit #5964 adapter) ── ESP32 DevKitC-32 (ESPHome)
                                                      │
                        Field-mode duty-cycle log to flash: always running
                        Dock-detect HIGH (home dock, USB charging, or solar):
                          triggers a bounded-window WiFi attempt (home WiFi or
                          Pixel hotspot) in the background — logging keeps
                          running until that attempt actually succeeds
                                                      │ MQTT (once connected)
                                                      ▼
                              Mosquitto broker (jctsh.duckdns.org:8883, TLS)
                                         │
                                         └──► Node-RED
                                                │ routes /log → Python log server
                                                │ watchdog on /heartbeat
                                                │ wildcard /data handler → Google Sheets
```

**MQTT topics:**
- `jctsh/components/air-quality-monitor/data`
- `jctsh/components/air-quality-monitor/log`
- `jctsh/components/air-quality-monitor/heartbeat` (home mode only)

**No SmartThings, no Home Assistant integration** — no real-time state to expose (per Phase 3 decision).

**Timeout policy — superseded 2026-08-20** (see `JCTsh-air-quality-monitor-phase1.md`'s JCTsh Integration table for the full decision history): the original 2026-07-09 decision assumed home mode only happens docked/charging at home, USB-powered — false, since solar and field USB charging share the dock-detect (`IN+`) signal with the home dock, so dock-detect can go HIGH mid-hike, on battery, with no home WiFi in range.

Current design: field duty-cycle logging runs unconditionally, independent of dock-detect state. Dock-detect HIGH only triggers a background WiFi connection *attempt* against both configured networks (`JCTnet1` and the Pixel hotspot — see the new `hotspot_ssid`/`hotspot_password` secrets), bounded to a target 2-minute window before disabling the WiFi radio (`wifi.disable`) rather than retrying indefinitely, then re-attempting periodically (target 15–20 minutes) for as long as dock-detect stays HIGH. No cap on the number of periodic retry cycles — only on how long each individual attempt window runs. Logging only pauses once WiFi **and** MQTT actually connect, at which point the device replays the SPIFFS backlog and switches to publishing live, exactly like hiking-monitor's home mode. Implementation (interval/lambda structure for the attempt window and radio disable/enable) is a Step 4/Step 8 task, not specified further here. Still explicitly does not inherit hiking-monitor's `wifi.ap:` + `reboot_timeout` bug interaction (CARD-0045) — confirm in Step 4 whether an `ap:` fallback block is actually needed before including one.

---

## Step 0 — Read Build Standards

**Claude Code does:**
Read `JCTsh-Build-Standards.md` in full. This build touches: §2 ESPHome standards (boilerplate, MQTT publishing patterns, GPIO assignment, deep-sleep/duty-cycle sequencing per §2.13), §2.10 onboard flash logging (field mode pattern), §2.14 battery safety standards, §3 MQTT standards, §4 observability standards, §8 LED indicator standards (RGB threshold pattern). Also read `components/hiking-monitor/` in full — this build must match its firmware pattern, not re-derive it. State explicitly which standards apply before writing any code or config.

**Joseph confirms:**
Acknowledged — proceed.

---

## BENCH PHASE

All steps in this section are performed on the workbench, on breadboard first per JCTsh-Build-Standards.md §1.2, before any perfboard transfer.

## Step 1 — Confirm mode-switching design

**Resolved 2026-08-19, revised 2026-08-27 (CARD-0218) — see Step 1 above and the Step 8 note below.** Dock-detect-only for firmware mode-switching is no longer the design. A real GPIO-readable Intent switch (repurposed slide switch, GPIO27) plus a separate inline Power Switch (new BK-1208 push button, no GPIO) now cover the two concerns this section originally split — see Hardware Context above for the full reasoning. GPIO table updated to add the GPIO27 row.

---

## Step 2 — Create MQTT account and secrets.yaml

**Claude Code does:**
Generate a strong random password, document the `mosquitto_passwd` command for the `air-quality-monitor` account (JCTsh-Build-Standards.md §2.11), create `secrets.yaml.template`, confirm `.gitignore` coverage.

**Joseph does:**
Run the account-creation command on the Pi; populate `secrets.yaml`.

**Joseph confirms:**
Account created, secrets file in place and untracked by git.

---

## Step 3 — Breadboard wiring

**Claude Code does:**
Create `wiring.md` and `ESP32-project-pins.md` (full 38-pin table) covering: I2C bus to the SEN55/adapter, the BC547B SEN55 power-gate circuit, the `battery_v` divider, the dock-detect divider (matching hiking-monitor's exact values), the MCP1700 LDO wiring (`VIN` to battery+ node in parallel with TP4056's `BAT+`, `VOUT` to ESP32 `3V3` directly, per the CARD-0026/CARD-0070 rig pattern), and the inline power switch (in-line on the battery+ path, ahead of both the TP4056 and the LDO tap point). Also document the perfboard footprint measurement procedure in `wiring.md` (SEN55 module + Adafruit adapter physical dimensions, laid out to determine minimum board size) — **for use at Step 9, not this step** (superseded 2026-08-20: measuring footprint this early was premature, before there's a real perfboard layout to size against; moved to where it's actually actionable).

**Joseph does:**
Wire on breadboard, powered via USB.

**Joseph confirms:**
Wiring complete.

**Claude Code does:**
Record the confirmed perfboard size in this doc and the BOM.

---

## Step 4 — ESPHome base config and SEN55 validation

**Claude Code does:**
Write the initial `air-quality-monitor.yaml` — standard boilerplate (§2.8), I2C bus, native `sen5x` sensor platform, standard `on_connect`/heartbeat MQTT patterns (§2.7). `wifi: networks:` lists both `wifi_ssid`/`wifi_password` and `hotspot_ssid`/`hotspot_password` (added 2026-08-20 — see Timeout policy above), matching hiking-monitor's pattern. `mqtt:` block uses `port: 8883` with `certificate_authority: !secret mqtt_ca_cert` (TLS, matching hiking-monitor's CARD-0003 config) — not plaintext 1883, now that `mqtt_broker` points at `jctsh.duckdns.org`. Resolve Step 1's mode-switching design into the `wifi:` block — per the timeout policy above, do not include a `wifi.ap:` fallback unless Step 1 established a real need for it.

**Joseph does:**
Flash via USB. Confirm PM/VOC/NOx readings on the log dashboard.

**Joseph confirms:**
All SEN55 fields reporting plausible values. **Met 2026-08-21 10:33 MST** — after a real multi-hour diagnostic session (see CARD-0012's kanban entry for the full trail): a firmware bug (`sen5x:` block missing its `id:`, referenced by `on_boot`) was found and fixed first, then an extensive hardware fault chase on the SEN55 power-gate transistor circuit (BC547B) — every individual component/connection checked out (resistor, base voltage, VIN, transistor swap, relocation, Collector/Emitter continuity) yet the circuit still wouldn't reliably power the sensor, eventually traced to an intermittent breadboard contact via the adapter's own power LED, though not fully/durably resolved. **Confirmed via the bypass jumper configuration** (adapter `GND` wired directly to common ground, bypassing the transistor entirely) — this is a legitimate, temporary substitute for the gate circuit specifically for the purpose of validating the SEN55/adapter/I2C wiring itself, which is genuinely proven now. The gate circuit itself remains unresolved and is deferred to Step 6, which now also inherits a real open design question (low-side vs. high-side switching) surfaced during tonight's debugging — see that step's updated notes.

---

## Step 5 — RGB LED threshold logic

**Claude Code does:**
Implement the PM2.5 → RGB color mapping (green <12, yellow 12–35, red >35 µg/m³) on GPIO18/19/23.

**Joseph does:**
Verify LED color changes correctly across the three PM2.5 ranges (can simulate with a known particulate source, or verify logic against manually-set test values).

**Joseph confirms:**
All three color states verified. **Green state met 2026-08-21 10:50 MST** — deployed cleanly, live PM2.5 at 2.0 µg/m³ correctly showing green. **Yellow and red states met 2026-08-21 11:53 MST** — verified via a boot-time color-hold sequence (solid Yellow 3s, solid Red 3s, added permanently rather than as a one-off test — Joseph's preference, confirms both colors on every boot without needing a real particulate source in range). Step 5 fully closed.

---

## Step 6 — SEN55 power-gate transistor bench test — DROPPED and CLOSED, 2026-08-21

**Design decision made and physical breadboard confirmed to match. Step 6 is closed.**

Step 4's diagnostic session had left this step inheriting a real open design question — low-side (BC547B) vs. high-side (P-FET) switching — after the BC547B gate circuit failed to reliably power the SEN55 across multiple boot cycles (see CARD-0012 kanban entry for the full trail). Revisiting *why* a gate was wanted at all resolved the question a different way:

- **Routine duty-cycling** (the original motivation — SEN55 draws ~63mA in Measurement mode, too much to leave running the whole hike): Sensirion's own "Reduced Power Operation for SEN5x" doc recommends I2C mode-switching (Measurement ↔ RHT/Gas-Only) as the primary power-saving mechanism, not physically cutting power. That's a Step 8 firmware task against the native `sen5x` platform, not a hardware gate.
- **True full-off** (storage/transport between hikes): already covered by the inline power switch (Hardware Context table, wired directly into the battery+ path, decided Step 1) — that's a whole-device cutoff, no SEN55-specific gate needed.

With both real use cases already covered elsewhere, there's nothing left for a dedicated GPIO27 gate to do — and dropping it also eliminates the low-side/high-side reliability question outright, along with the exact failure mode (marginal GND-return connection silently breaking I2C) that caused Step 4's multi-hour diagnostic session. The former "bypass jumper" (adapter `GND` directly to common ground) is now the permanent design, not a workaround — reflected in `air-quality-monitor.yaml`, `wiring.md`, and the Hardware Context/GPIO tables above. GPIO27 is unused. BC547B/BS250 stock remains on hand, unused by this build.

**Claude Code does:**
Update all build docs to remove the gate-transistor design (done — this entry, Hardware Context table, GPIO table, `air-quality-monitor.yaml`, `wiring.md`).

**Joseph does:**
Update the physical breadboard to match: remove the BC547B transistor, its 1kΩ base resistor, and its 10kΩ base pull-down resistor from the circuit entirely (not just set aside — they were already "set aside, not removed" once before, during Step 4, which is part of how the board ended up in an ambiguous state). Confirm the SEN55 adapter's `GND` pin has a solid, direct connection to the common ground rail — not the original diagnostic-session jumper left in place by chance, but a wire placed deliberately as the permanent design. GPIO27 (pin 11) should have nothing connected to it.

**Joseph confirms:**
**Met 2026-08-21 12:50 MST.** Transistor and both resistors physically removed from the breadboard; SEN55 `GND` verified as a direct, solid connection to common ground; GPIO27 confirmed unconnected. Step 6 closed.

---

## Step 7 — LiPo polarity check and power validation

**Unblocked 2026-09-08 — CARD-0198 closed.** The power design is now settled and validated: Pololu D24V10F3 regulator swap and CARD-0218's Intent/Power-switch redesign are both physically built, and CARD-0198's staged `minimal-test.yaml` sequence confirmed both of the device's real operating modes (field: battery + SEN55 alone; docked: TP4056 + battery + WiFi/MQTT/SEN55) stable. Two real findings from that testing carry directly into this step, below: the power switch needed rewiring to actually do its job, and the low-battery cutoff needs real margin. The text below reflects the target hardware; part names and wiring have been updated accordingly.

**Power switch rewiring, added 2026-09-08 (CARD-0198's own finding, folded in here rather than a separate card since Build is already in progress).** The switch's real job is to let a person force a full cold restart on demand (not primarily storage/transport off, which is a bonus) — but CARD-0198 measured that the original wiring (switch directly in the LiPo's own leg, upstream of a node TP4056 could also feed from USB) fails at exactly that job whenever docked: TP4056's own charge output backfeeds the shared node regardless of switch position, so switching off while docked doesn't actually remove power from the ESP32. **Rewire so the switch gates only the Pololu's `VIN`**, with LiPo `BAT+` and TP4056 `BAT+` tied together directly upstream of it — see `wiring.md`'s "Inline Power Switch" section for the full new diagram and reasoning. Side benefit: charging now works even with the device switched off, which it couldn't before.

**Claude Code does:**
Document the JST polarity verification procedure (same requirement as hiking-monitor) before first battery connection. Include confirming the Pololu D24V10F3's `VOUT` reads a clean 3.3V under load and the BK-1208 power switch (now wired per the rewiring above, gating only the Pololu's `VIN`) actually breaks the circuit in both positions — **measure for zero voltage/current at the Pololu's `VIN` pin with the switch off, both with USB unplugged from TP4056 and with USB plugged in.** The USB-plugged-in check is the one CARD-0198's original verification instruction missed — it would have passed under the old wiring with USB unplugged and silently failed with it plugged in, exactly the gap that testing found the hard way. Also confirm TP4056's charge LED still indicates charging with the switch off and USB connected, direct proof charging no longer depends on switch position. Note that this switch is what satisfies `wiring.md`'s "never power from USB and the regulator at the same time" caution — switching it off removes the regulator's `VIN` entirely, equivalent to unplugging it, so USB flashing just requires the switch off rather than any physical disconnect. This isn't a one-time Step 7 concern: once the battery/regulator are wired in here, it applies to every subsequent USB connection for the rest of the build and field life of the device — Step 8's and Step 9's USB flashes below, and any future re-flash over USB, all need the switch off first.

**Dock-detect, battery-divider, and Intent-switch raw checks belong here, not Step 8.** All three signals were wired before Step 8 needs them, but none has been checked on its own — dock-detect and the Intent switch would otherwise only get exercised buried inside Step 8's much more complex WiFi-attempt/gating logic, and the battery divider is still reading off the 3.3V rail placeholder rather than the real LiPo. Step 7 is when the real battery goes in and USB gets connected/disconnected anyway, so it's the cheap, isolated place to confirm all three raw signals before Step 8 adds behavior on top of them.

**Joseph does:**
Verify polarity, connect the EEMB LiPo pouch to the TP4056 module, confirm normal charge behavior (TP4056 side, now upstream of the switch) and normal 3.3V power delivery via the Pololu D24V10F3 regulator (not the boost module's old 5V→onboard-regulator path). Confirm the BK-1208 power switch cuts power cleanly in both directions — including the USB-plugged-in check above. **Battery divider:** first **rewire R1's top leg from the 3.3V rail placeholder to the real LiPo `BAT+` (post-switch, i.e. the Pololu `VIN` side)** — per `wiring.md`'s Battery Voltage Divider Wiring section, this move was always deferred to "when the power system is integrated," which is now — then compare the `battery_v` sensor's logged value (heartbeat or serial log) against a multimeter reading taken directly at the battery terminals to confirm they're close (the 100kΩ/100kΩ divider's `multiply: 2.0` filter should reconstruct the true battery voltage). **Dock detect:** connect and disconnect USB (or briefly bridge the divider's input node to 3.3V, if easier) while watching the serial log during an `esphome run` session — confirm `dock_detect`'s logged state flips HIGH/LOW as expected, independent of any WiFi-attempt behavior (that's Step 8's concern, not this check's). **Intent switch:** toggle the SS12D10 (now on GPIO27) while watching the serial log — confirm it reads LOW when closed/ON and HIGH (via internal pull-up) when open/OFF, independent of any WiFi-gating behavior (also Step 8's concern, not this check's).

**Joseph confirms:**
Polarity correct, battery connected, regulator delivering clean 3.3V, BK-1208 switch verified to actually cut power in both positions with USB both unplugged and plugged into TP4056 (not just visually "off"), TP4056 charge LED confirmed still active with the switch off, everything functioning normally. Battery divider reading confirmed close to a direct multimeter measurement. Dock-detect confirmed flipping HIGH/LOW correctly in the serial log on USB connect/disconnect. Intent switch confirmed flipping LOW/HIGH correctly in the serial log on toggle.

---

## Step 8 — Field/home mode duty-cycle and WiFi replay firmware

**Claude Code does:**
Implement the field-mode duty-cycle logging via **I2C mode-switching** (Measurement ↔ RHT/Gas-Only, per Step 6's 2026-08-21 decision — not physical power-gating, since SEN55 is now hard-wired always-on). Reconcile timing against Sensirion's own guidance surfaced during that decision: a **30–60s warm-up** is recommended after leaving RHT/Gas-Only mode for good PM accuracy (8s is documented as an absolute floor, not a target) — longer than the Phase 1 power budget's original ~10s active window per 2-minute cycle, so confirm the actual cycle timing against this before locking it in, not the old assumption. Reading via the native `sen5x` platform, logged to flash via the adapted `hiking_logger.h` pattern — **this runs unconditionally, independent of dock-detect state** (superseded 2026-08-20 Timeout policy decision above; deviates from hiking-monitor's exact pattern, which stops field logging as soon as dock-detect goes HIGH — call this deviation out explicitly in code comments so a future reader doesn't assume it's identical).

**Corrected 2026-08-27 (CARD-0218), superseding the bounded-retry design originally planned here — see `JCTsh-Build-Standards.md` §2.14 point 11. This surfaces a real, unresolved architecture gap for this specific device, not just a design tweak.** Dock-detect HIGH must not trigger a WiFi attempt on its own — dock-detect is shared with solar (same IN+/IN- pads as USB), and solar connecting mid-session says nothing about network availability, so trying is never justified while still actively collecting, full stop, same as hiking-monitor's corrected rule.

**Resolved 2026-08-27, same day this was flagged — this device now has a real Intent signal, not just a diagnosis of the gap.** Interviewed through several switch-design candidates (guarded/recessed toggle — too bulky/enclosure-complex; mini rotary — solid option, superseded) before landing on the same part chosen for hiking-monitor's own missing-signal gap (CARD-0181): a **BK-1208 latching push button** takes over the Power Switch role, freeing the existing SS12D10 slide switch to become a real, GPIO-readable **Intent switch on GPIO27** — matching hiking-monitor's exact pin/pattern. `wifi.enable()` in Step 8's firmware should be gated on this Intent switch being off (session genuinely over), exactly like hiking-monitor's corrected `dock_detect` handler above — never on `dock_detect` alone. See the Hardware Context table's "Inline power switch" and "Intent switch" rows for the full wiring detail, and `JCTsh-Build-Standards.md` §2.14 point 12 for why two distinct physical controls were needed rather than one.

**Third gating condition added 2026-09-08, from CARD-0198's live testing — "sufficient power," not just "network available."** Intent-off + Power-Connected-true was always meant to answer "is a network reachable," but CARD-0198 found that's not the same question as "is it safe to actually attempt the upload." A real battery-only trial degraded into a self-sustaining brownout-reset loop once voltage sagged to the Pololu's documented 3.4V floor — the same number the standard low-battery firmware cutoff already used, leaving zero real margin by the time it fired. **`wifi.enable()` must therefore also require battery voltage above a new, real-margin threshold**, meaningfully higher than 3.4V. All three conditions (Intent off, Power Connected true, voltage above the upload-safe margin) are required together; any one false means keep buffering, don't attempt.

**One item resolved, one still open:**
1. **Decided 2026-09-08 (Joseph): separate and additional, not a replacement.** The existing generic low-battery shutdown cutoff (§2.14 point 2, protects the LiPo cell from over-discharge) is unchanged — field mode keeps collecting and buffering at low current all the way down to that floor, same as any other JCTsh device. The new upload-safe threshold is a second, higher, narrower gate that applies only to attempting WiFi/MQTT — a device sitting below the upload threshold but still above the general safety cutoff just keeps logging and buffering, waiting for voltage to recover (get docked/charged) or for the general cutoff to eventually shut it down. It's never forced to stop collecting early just because uploading isn't currently safe.
2. **Provisional value set 2026-09-08: 3.8V — not yet confirmed by a real bench sweep, treat as a placeholder.** Estimated from the data on hand rather than measured directly: 3.4V (measured mid-loop) is confirmed catastrophic — zero regulator headroom, a sustained non-recovering brownout loop; ~3.86-3.88V (2026-08-28, battery alone) still showed occasional single-brownout-then-recover on WiFi association, not fully clean; TP4056-alone (zero battery contribution) was rock-solid 4/4 clean across all three combined-load stages today, suggesting real spare capacity once docked. 3.8V sits meaningfully above the catastrophic floor and errs toward the safer side of the asymmetry: an underestimate risks a real, hands-on-intervention-required lockup (worse) versus an overestimate only costing delayed uploads (milder) — see this card's own discussion for the full reasoning, folded in here as design rationale. Confirm with a real bench sweep at the first practical opportunity (trigger a WiFi+SEN55 burst at several voltages on the rewired hardware, find where it actually stops brownouting) — same empirical method CARD-0198 used for everything else in this investigation — and revise this number once real data exists; a real device's first natural approach to this threshold in the field is also a free data point worth capturing. **Caution, found 2026-09-08 during Step 7's own verification:** every voltage reading (bench sweep or runtime) must be taken with the charger disconnected — a battery's terminal voltage reads artificially high while TP4056 is actively charging it (the charging current itself elevates the reading against the battery's own internal resistance), so a "voltage" logged while docked doesn't reflect the battery's true state of charge. Confirmed live: 3.9V measured at the switch's input while the charge LED was lit, but unplugging USB and letting the battery actually supply the Pololu dropped `VOUT` to 3.18V — the real, load-bearing voltage was well below what the mid-charge reading suggested.

Once WiFi **and** MQTT actually connect (whether via `JCTnet1` at home or the hotspot in the field), switch to home-mode behavior: replay the SPIFFS backlog to MQTT using original timestamps, then publish new readings live instead of buffering (per hiking-monitor's exact pattern from that point on). Include the 5-minute heartbeat in home mode only.

**CARD-0218 (2026-08-27): the real `/data` payload built here must include `temp_f`/`humidity_pct` from the SEN55's own `sen55_temp`/`sen55_humidity` sensors**, not just PM/VOC/NOx/battery — those two fields exist specifically so this device's readings can serve as an independent reference to compare against hiking-monitor's BME280 (mounting/placement may make this device's reading more accurate) — pointless if they never leave the device. Same `source: air-quality-monitor` / field-naming convention every other source already uses in the Environmental Data schema, no special-casing needed. `/data` field set (Environmental Data Schema): `temp_f`, `humidity_pct`, `pm1_ug_m3`, `pm25_ug_m3`, `pm4_ug_m3`, `pm10_ug_m3`, `voc_index`, `nox_index`, `battery_v`, `rssi_dbm`, `lat`/`lon` always null (no GPS hardware).

**Design finalized 2026-09-09, working through the mechanics in detail before writing code — five pieces:**

**1. SEN55 duty-cycle mode-switching.** 2-minute cycle (matches this project's standard sensor cadence). Idle in RHT/Gas-Only mode (`SEN5X_CMD_START_MEASUREMENTS_RHT_ONLY = 0x0037` — confirmed directly from the installed ESPHome package's `sen5x.cpp` source, not guessed) for most of the cycle; ~40s before each reading (within Sensirion's recommended 30-60s warm-up window), switch to full Measurement mode (`0x0021`), read PM/VOC/NOx/temp/humidity, then drop back to RHT-only. The warm-up wait is implemented as a loop of short delays with `App.feed_wdt()` fed each iteration (same discipline as `hike_log_replay_stream`'s per-line feed, CARD-0211) — never one giant blocking `delay()`, which risks tripping the task watchdog.

**2. WiFi never gets a free pass at boot — same latent gap CARD-0217 found and fixed on hiking-monitor.** ESPHome's `wifi:` component tries to associate automatically and unconditionally during its own `setup()` — nothing in this file today tells it not to, exactly hiking-monitor's pre-CARD-0217 state. **This device gets the fix at boot, not deferred to the first interval tick like hiking-monitor needed to.** Checked the actual priority ordering rather than copying hiking-monitor's pattern blind: hiking-monitor's gate-setting `on_boot` block is priority 600 (runs *before* WiFi's fixed `setup_priority` of 250, so `wifi.disable()` there would be unsafe — hence its deferral to the interval). This file's existing `on_boot` block is priority **-100** — since -100 < 250, WiFi's `setup()` has already completed by the time this block runs. The three-condition gate check (Intent off AND Power Connected AND battery ≥ 3.8V) becomes the literal first action in this `on_boot` block, before the existing SEN55-idle/LED sequence — `wifi.disable()` fires within milliseconds of boot if the gate isn't met, not after the ~60-80s the existing SEN55/LED/bounded-wait sequence would otherwise take. **The existing bounded 30s MQTT-wait loop only runs when the gate is true** — skipped entirely when it's false, since there's no legitimate attempt in progress to wait for.

**3. Bounded attempt window + retry backoff (`JCTsh-Build-Standards.md` §2.14 point 13, Step 2) — reference numbers: ~2min window, ~15min retry, both soft targets checked at 2-min granularity** (reusing the existing 2-min interval tick for this state machine too, same precedent as CARD-0224's periodic recheck on hiking-monitor — "this tick already runs every 2min regardless of mode, so it's the natural place to re-check... rather than a separate timer"). Two timestamps + one boolean (`wifi_attempt_start_ms`, `wifi_last_attempt_end_ms`, `wifi_attempt_in_progress`), checked every tick:
   - Gate false → `wifi.disable()` immediately if enabled, clear all attempt state.
   - Gate true, MQTT connected → nothing to do, `on_connect` already took over.
   - Gate true, MQTT not connected, no attempt tracked → start one: either a genuinely new opportunity (`wifi.enable()`, stamp start time) or *adopting* WiFi's own already-running boot-time attempt (stamp start time without re-calling `wifi.enable()`, since it's already on).
   - Gate true, attempt in progress, window not yet elapsed → wait.
   - Gate true, attempt in progress, window elapsed (~2min) → `wifi.disable()`, stamp end time, clear in-progress flag.
   - Gate true, no attempt in progress, previous attempt ended → wait for ~15min since that end time, then loop back to "start one." No cap on retry count — only on each individual window's duration, per the instructions doc's existing Timeout policy text above.

**4. LED diagnostics — Blue is the dedicated networking-status channel, since PM2.5's threshold indicator never uses it and Red/solid-Blue are already spoken for by the reset-reason check.** Decided 2026-09-09, dropped the "not attempting" case (Intent on, or no power — the common/expected case, low diagnostic value against the cost of a blink every boot):
   | State | Pattern | When (elapsed since power-on) | Duration |
   |---|---|---|---|
   | Attempting blocked — docked, Intent off, but battery < 3.8V | blue+red together, 3 blinks | first action in `on_boot`, effectively immediately | ~1.8s |
   | Actively attempting WiFi/MQTT (gate true) | slow blue blink, ~1/sec | starts once the bounded-wait section is reached (~7-10s in, after the existing reset-reason + self-test sequence) | up to 30s, or shorter if it connects sooner |
   | Connected | solid blue | whenever it succeeds within the window | ~1s |
   | Gave up, retrying in ~15min | 2 quick blue blinks | at the 30s mark, if it never connected | ~0.6s |

   Practical guidance for watching the device at the bench: the voltage-blocked pattern (if it fires) happens in the **first ~2 seconds** — easy to miss if not already watching. If nothing blue happens in that window, the gate was true; watch for the slow blink starting **~7-10 seconds** in, resolving to either solid blue or the double-blink within the next 30 seconds.

**5. Matching MQTT log messages — buffered for three of the four states, live for one.** The voltage-blocked, attempting-start, and gave-up-timeout states all occur before (or without) a connection existing by definition, so they can't be published live — they're buffered via the flash-log mechanism (same as CARD-0195's skip/reset events on hiking-monitor: `{"event":"wifi_attempt_blocked", "battery_v":...}` / `{"event":"wifi_attempt_timeout"}`, replayed alongside real readings once a connection eventually happens, requiring a matching Node-RED routing addition to `environmental-data.flow.json`'s existing "Route skip/reset events" function node). Only "connected" can log live — extend the existing `on_connect` message.

**Joseph does:**
Switch the inline power switch off before connecting USB (battery/LDO are wired in as of Step 7 — see that step's note), then flash via USB, simulate a field session (undock, wait through a few duty cycles) then redock and confirm replay. Additionally test the new field-WiFi-attempt path: with the device undocked and running on battery, trigger dock-detect (e.g. connect USB or solar) with no `JCTnet1`/hotspot in range, and confirm logging continues uninterrupted through at least one full attempt-window-then-backoff cycle rather than stalling.

**Joseph confirms:**
Field-mode logging and home-mode replay both work as expected, matching hiking-monitor's proven behavior — plus the new bounded-retry behavior confirmed not to interrupt logging or get stuck when no network is reachable.

---

## Step 9 — Perfboard footprint measurement and transfer

**Claude Code does:**
N/A until Joseph reports the footprint measurement below — then create `perfboard-layout.md` using it.

**Joseph does:**
**First, measure the footprint** (moved here 2026-08-20 from Step 3, where it was premature): follow `wiring.md`'s Perfboard Footprint Measurement Procedure — physically measure the SEN55 module + Adafruit #5964 adapter, lay out the full component set, and confirm whether the standard 5×7cm Chanzon FR4 board (Bag 9) is sufficient. **Working assumption: the same 5×7cm size hiking-monitor uses will probably work here too** (`hiking-monitor/perfboard-layout.md` confirms that's what it used) — treat the measurement as confirming/adjusting that assumption, not starting from zero. Report the result back.

Then transfer the validated breadboard circuit to perfboard: ESP32 + SEN55/adapter + Pololu D24V10F3 regulator (+ bulk caps) + BK-1208 power switch + SS12D10 Intent switch + debug UART header + RGB LED + both dividers. No gate transistor (dropped Step 6). Continuity-check before power-on. Switch off before connecting USB for any post-transfer USB flash/debug, same as Step 8.

**Joseph confirms:**
Footprint measured, perfboard size confirmed (or corrected from the 5×7cm assumption); perfboard build complete, device boots and operates identically to the breadboard version.

---

## Step 10 — Heartbeat/watchdog registration

**Claude Code does:**
Confirm the existing Node-RED watchdog wildcard subscription and `/data` wildcard handler catch this device automatically — no new flows needed.

**Joseph does:**
Confirm in the Node-RED editor and Google Sheets.

**Joseph confirms:**
Device appears in the watchdog's tracked component list; readings appearing in the Environmental Data sheet after a simulated home-mode sync.

---

## Bench Phase Complete — Install Phase Begins

All bench steps above are confirmed complete. The device has been:
- Fully wired and perfboard-built with the SEN55/adapter, power-gate transistor, RGB LED, and both dividers
- Validated on USB power and on battery power
- Running field-mode duty-cycle logging and home-mode WiFi replay, matching hiking-monitor's proven pattern
- Integrated with the log dashboard, watchdog, and Google Sheets

Do not proceed to any install/carry-case work until every bench step above is confirmed complete.

---

## INSTALL PHASE

**Deliberately not detailed in this instruction set** — same split as hiking-monitor (CARD-0009) and remote-temp-sensor-01. Enclosure/carry-case design depends on measurements and confirmations this bench phase produces (actual perfboard footprint, confirmed power-gate transistor behavior, confirmed mode-switching design) that don't exist yet.

See "Future Enhancement" below.

---

## Future Enhancement — Clip Case Enclosure

**Planning started 2026-08-20** — `air-quality-monitor-enclosure-plan.md` captures what's already decided and the open questions still needing physical measurement, following the same process used for `hiking-monitor-enclosure-plan.md`/`hiking-monitor-enclosure-instructions.md`. CAD work itself does not begin until the bench phase below is confirmed complete.

Once the bench phase above is complete, open a follow-on planning pass covering:
- 3D-printed clip case with carabiner attachment, independent of hiking-monitor's own enclosure
- ~~Air intake/exhaust port placement for the SEN55 fan~~ **Moot — resolved 2026-08-20.** SEN55 mounts externally via 3M double-sided foam tape to the enclosure's smooth outer surface (its own sealed metal housing/fan shield handles airflow directly from ambient, not through the JCTsh enclosure), cabled to the internal Adafruit #5964 adapter via the existing 100mm JST-GH cable. No custom venting to design; the low-confidence Sensirion orientation research no longer needs re-verification for this build.
- **New:** small cable pass-through hole for the SEN55's JST-GH cable, sized/positioned so the sensor sits flush against the exterior mounting point — same pattern as the solar JST exit hole
- White ASA for final print (corrected 2026-08-20 from Phase 1's original PETG call — matches hiking-monitor's own upgrade for Tucson UV/heat resistance) to minimize solar gain
- Micro USB charging port and external JST solar port placement (SUNYIMA panel, backpacking use)
- Screw/fastening hardware — confirm actual length needed once enclosure dimensions exist, same caution as remote-temp-sensor-01 and hiking-monitor (don't assume on-hand kit screws are long enough)

## Future Enhancement — Deferred Features (from Phase 1)

| Feature | Status |
|---|---|
| Bluetooth/real-time data share to hiking monitor display | Evaluated and deferred — added field-failure modes not justified by the data value |
| NOx threshold LED indicator | Deferred — VOC index covers field awareness adequately; NOx is more useful in post-hike Sheets analysis |
| Solar panel mount/clip design | Deferred to the enclosure design phase above |
| Disable onboard power LEDs (ESP32 red PWR LED, Adafruit #5964 adapter green "on" LED) | Deferred, for consideration later. Adapter LED has a documented cuttable trace on the back silkscreened "LED" (learn.adafruit.com/adafruit-sen54-or-sen55-adapter-breakout/pinouts) — cut with a hobby knife, reversible by re-bridging with solder. ESP32 DevKitC-32's red PWR LED has no such jumper — disabling it means desoldering the series resistor (or the LED itself), real SMD work for a few mA of savings. Revisit at Step 7 (battery install) or Step 9 (perfboard transfer), when the board is already being handled directly. |

---

## Notes for Claude Code

- Step 0 is mandatory: read `JCTsh-Build-Standards.md` in full and `components/hiking-monitor/` in full before writing any code — this build must match hiking-monitor's pattern, not re-derive it
- SEN55 uses ESPHome's native `sen5x` platform — do not write a custom component for the sensor itself
- Custom component is still needed for onboard flash logging + WiFi replay — adapt `components/hiking-monitor/hiking_logger.h`, do not rewrite from scratch
- Do not copy hiking-monitor's `wifi.ap:` fallback block without confirming it's actually needed (CARD-0045) — if included, be aware `reboot_timeout` may not function as expected
- Log format: JSON to `jctsh/components/air-quality-monitor/log`
- `lat`/`lon` are always `null` in this payload — no GPS hardware, timestamp correlation with GaiaGPS/hiking-monitor happens post-hike
- `rssi_dbm` is 0 for field-mode readings (no WiFi at time of logging) — same convention as hiking-monitor
- MQTT account: create dedicated `air-quality-monitor` Mosquitto account before first flash
- Add new account to credentials table in root `CLAUDE.md`
- Record new device IP, hostname, and MAC in `network/jctsh-network.md` once ready to flash
- Update `jctsh-parts-inventory.md` at the end of the bench phase — deduct all used parts, record the Step 6 measured power-gate current
- Bench-first: all bench steps must be confirmed complete before any install-phase work begins
