joscthomas/jctsh/components/hiking-monitor/wiring.md

# Hiking Monitor — Breadboard Wiring Reference
**Component:** hiking-monitor
**Purpose:** Complete wiring reference for the ESP32 breadboard prototype.

---

## Before Wiring

**ESP32 pin label orientation:** ESP32 DevKit pin labels face **down** when the board is inserted in a breadboard — the text is on the underside. Mark key GPIO rows with masking tape labels on the breadboard before wiring to avoid pin confusion.

Rows to label: GPIO4, GPIO5, GPIO16, GPIO17, GPIO18, GPIO21, GPIO22, GPIO23, GPIO32, GPIO35

GPIO32 note: configured as INPUT (no pull-up or pull-down) — the dock detect voltage divider provides defined state.

Copy `components/garage-radar/ESP32pins.png` to this directory for reference during wiring.

---

## GPIO Assignment Summary

| GPIO | Function | Component |
|---|---|---|
| GPIO4  | BUSY (input) | E-ink display |
| GPIO5  | SPI CS (active-low) | E-ink display |
| GPIO16 | RST (active-low reset) | E-ink display |
| GPIO17 | DC (data/command select) | E-ink display |
| GPIO18 | SPI CLK | E-ink display (VSPI) |
| GPIO21 | I2C SDA | BME280 + LTR-390 (shared) |
| GPIO22 | I2C SCL | BME280 + LTR-390 (shared) |
| GPIO23 | SPI MOSI / DIN | E-ink display (VSPI) |
| GPIO32 | Dock detect (divider midpoint, INPUT) | TP4056 IN+ → 68kΩ → midpoint → 100kΩ → GND |
| GPIO35 | Battery ADC (input-only) | Voltage divider midpoint |

---

## BME280 (GY-BME280) Wiring

| BME280 Pin | Wire color | ESP32 Pin | Notes |
|---|---|---|---|
| VCC | Red | 3.3V | The GY-BME280 has an onboard voltage regulator — connect to 3.3V, not 5V/VIN |
| GND | Black | GND | |
| SDA | Yellow | GPIO21 | I2C data — shared with LTR-390 |
| SCL | Blue | GPIO22 | I2C clock — shared with LTR-390 |

I2C address: 0x76 (SDO/CSB pin is tied to GND on GY-BME280 breakout).

---

## LTR-390 UV Sensor Wiring

**Updated (2026-07-12, CARD-0009 enclosure rework):** the sensor-side connection now uses a STEMMA QT / Qwiic cable (Adafruit #4209, JST SH 4-pin to premium male headers, 150mm — `jctsh-parts-inventory.md` Bag 31) plugged directly into the LTR-390 breakout's STEMMA QT port, instead of soldered 0.1" male headers on the through-hole pads. The 150mm length gives slack to mount the sensor at the correct sky-facing orientation in the enclosure independent of the perfboard's own orientation. The male-header end plugs into the perfboard's existing LTR-390 female header (unchanged from the original build) — only this sensor-side segment changed; the perfboard-to-ESP32 traces/jumpers are untouched, still GPIO21 (SDA) / GPIO22 (SCL) per `ESP32-project-pins.md`.

**STEMMA QT cable colors (Adafruit standard — different from the old breadboard colors below):**

| LTR-390 Pin | Wire color | Connects to | Notes |
|---|---|---|---|
| VIN | Red | Perfboard header VIN pin | 3.3V |
| GND | Black | Perfboard header GND pin | |
| SDA | Blue | Perfboard header SDA pin | I2C data — shared with BME280 |
| SCL | Yellow | Perfboard header SCL pin | I2C clock — shared with BME280 |
| INT | — | (not connected) | Interrupt pin — not broken out on STEMMA QT, still unused |

**Gotcha:** the STEMMA QT cable's SDA/SCL colors are swapped from the old breadboard-era wiring below (Blue=SDA now vs. Yellow=SDA before). Wire by pin label, not by color, when connecting either end.

I2C address: 0x53 (fixed — no configurable address pin).
No I2C address conflict with BME280 (0x76 ≠ 0x53).

**LTR-390 placement:** Must face open sky during hikes. In the final enclosure it mounts on the top face, now via the STEMMA QT cable rather than being rigidly plugged into the perfboard. During bench testing, point at a sunlit window or outside to confirm UV readings change.

---

**Original breadboard-era wiring (superseded 2026-07-12, kept for history):**

| LTR-390 Pin | Wire color | ESP32 Pin | Notes |
|---|---|---|---|
| VIN | Red | 3.3V | Adafruit breakout has onboard 3.3V regulator — VIN accepts 3.3V directly |
| GND | Black | GND | |
| SDA | Yellow | GPIO21 | I2C data — shared with BME280 |
| SCL | Blue | GPIO22 | I2C clock — shared with BME280 |
| INT | — | (not connected) | Interrupt pin — not used |

**LTR-390 breadboard preparation (superseded):** The Adafruit LTR-390 (#4831) has STEMMA QT / Qwiic connectors, not standard 0.1" headers. Before breadboard use, solder standard 0.1" male header pins to the through-hole pads on the breakout board. The through-holes are labeled: VIN, GND, SDA, SCL, INT. Solder a 4-pin or 5-pin header strip to VIN/GND/SDA/SCL (INT is optional).

---

## Waveshare 2.13" E-Ink Display (V4, SSD1680) Wiring

The Waveshare V4 HAT is designed for a Raspberry Pi 40-pin header. For the ESP32, wire directly to the display's SPI + control pins using the FPC connector or via the HAT's pin header, connecting individual wires to the ESP32 breadboard.

**Use the labeled connector — not the 40-pin Pi header.**

The HAT has a connector with pre-attached color wires, each labeled. Connect each wire directly to the corresponding ESP32 breadboard row:

| Wire color | Label | ESP32 pin |
|---|---|---|
| Grey | VCC | 3.3V |
| Brown | GND | GND |
| Blue | DIN | GPIO23 pin 37 |
| Yellow | CLK | GPIO18 pin 30 |
| Orange | CS | GPIO5 pin 29  |
| Green | DC | GPIO17 pin 28 |
| White | RST | GPIO16 pin27  |
| Purple | BUSY | GPIO4 pin 26  |

**Notes:**
- Display operates at 3.3V logic — no level shifting needed with ESP32.
- Keep wires short and tidy — SPI signals can be noise-sensitive at breadboard distances.
- The 40-pin Pi GPIO header on the HAT is not used.
- On the perfboard harness header, grey (VCC) is pin 1 — marked with a yellow dot.

---

## TP4056 Perfboard Connector (4-pin)

The TP4056+boost module connects to the main perfboard via a 4-pin female Dupont housing. Pin 1 is marked with a yellow dot on the perfboard header.

| Pin | Signal | Wire color | Destination |
|---|---|---|---|
| 1 (yellow dot ●) | IN+ | Green | R3 (68kΩ) top leg — dock detect divider input |
| 2 | BAT+ | White | R1 (100kΩ) top leg — battery voltage sense divider input |
| 3 | VOUT− (GND) | Black | ESP32 GND (left pin 14) via power-in header |
| 4 | VOUT+ | Red | ESP32 VIN (left pin 19) via power-in header — 5.7V boost output |

**Charge status LEDs, confirmed 2026-09-16 (Joseph) — closes a gap this project's own history had flagged as unconfirmed (see `components/air-quality-monitor/CLAUDE.md`, CARD-0012's Step 9 bench notes, which only speculated the generic "red=charging/green=complete" convention).** This module has two onboard LEDs: **red = power present** (lit whenever USB/solar is actually delivering power to the module, regardless of charge state), **green = charging** (lit while the battery is actively charging; goes off once charging is complete).

---

## Dock Detect Wiring (GPIO32)

TP4056 IN+ (USB VBUS) is divided down to a safe GPIO level. Measured values: 0.47V (USB absent), 5.1V (USB present).

```
TP4056 IN+ (green) ──── R3 (68kΩ) ──┬──── R4 (100kΩ) ──── GND
                                     │
                              GPIO32 (green, INPUT, no pull)
```

After divider:
- USB absent: 0.47V × 100/(68+100) ≈ **0.28V → LOW** (field mode)
- USB present: 5.1V × 100/(68+100) ≈ **3.04V → HIGH** (docked/charging)

| Connection | Notes |
|---|---|
| TP4056 IN+ → R3 (68kΩ) → midpoint | Top half of divider; green wire |
| Midpoint → R4 (100kΩ) → GND | Bottom half; ensures LOW when IN+ absent |
| Midpoint → GPIO32 | Green wire; no pull-up or pull-down — divider provides defined state |

On breadboard: R3 and R4 are through-hole resistors placed in the breadboard. Run a jumper from the TP4056 IN+ pin to R3, a jumper from R4 to GND rail, and a jumper from the midpoint to the GPIO32 breadboard row.

---

## Battery Voltage Divider Wiring

Divides LiPo voltage (3.5–4.2V) to fit ESP32 ADC range (0–3.9V at 11dB attenuation).
Using two equal resistors: R1 = 68kΩ (top), R2 = 68kΩ (bottom) → 2:1 divider.
Midpoint voltage = Vbatt / 2. ESPHome `filters: - multiply: 2.0` restores actual voltage.

```
TP4056 BAT+ (white) ──── R1 (100kΩ) ──┬── R2 (100kΩ) ──── GND
                                       │
                               GPIO35 (white, ADC input)
```

**Notes:**
- During breadboard testing without LiPo connected: wire the divider from the 3.3V rail instead of battery+ as a placeholder. Reads ~1.65V (scaled to ~3.3V in ESPHome). Replace with actual battery+ when power system is integrated in Step 8.
- High-value resistors (100kΩ) minimize current draw — total draw from divider is only ~40µA at 4V (3.7V / 200kΩ). Acceptable for battery-powered use.
- GPIO35 is an input-only pin — do not drive it as output. ADC use only.

---

## Slide Switch Wiring (GPIO27)

The slide switch signals hiking mode to the ESP32. It is not in the power path — the ESP32 runs continuously and uses deep sleep when not hiking.

| Switch terminal | Wire color | ESP32 pin | Notes |
|---|---|---|---|
| Terminal 1 | Brown | GPIO27 (left pin 11) | Switch ON (closed) pulls GPIO27 LOW |
| Terminal 2 | Black | GND | |

Switch ON (closed): GPIO27 pulled LOW → hiking/data-collection mode. ON position marked with yellow dot ●.
Switch OFF (open): GPIO27 floats HIGH via internal pull-up → sleep or upload mode.

**Breadboard wiring:** Run a brown jumper from one switch terminal to the GPIO27 breadboard row and a black jumper from the other terminal to the GND rail. The switch can sit on the breadboard directly or be held off-board with loose wires during testing — either works for bench verification.

**Perfboard:** brown wire connects to a 2-pin header pin 1 (GPIO27); black wire connects to the GND rail.

---

## Power (Breadboard Phase — Steps 4–7)

Power ESP32 via USB-C cable from PC during all breadboard testing (Steps 4–7). Do NOT connect LiPo until Step 8 (power system integration with polarity verification).

Power wiring for Steps 4–7:
- USB-C → ESP32 USB-C port (powers ESP32 from PC)
- Breadboard power rails: 3.3V from ESP32 3.3V pin → red rail; GND from ESP32 GND → blue rail

---

## I2C Bus Notes

Both BME280 and LTR-390 share the same I2C bus (GPIO21 SDA, GPIO22 SCL). This is supported — each device has a unique I2C address. The GY-BME280 and LTR-390 breakout boards include onboard pull-up resistors on SDA/SCL. No external pull-ups needed (two sets of pull-ups on a shared bus is acceptable at these speeds).

Enable `scan: true` in the ESPHome `i2c:` block during initial testing to confirm both devices are detected. Confirm in the ESPHome log:
```
[I][i2c.arduino:069]: Found i2c device at address 0x53  ← LTR-390
[I][i2c.arduino:069]: Found i2c device at address 0x76  ← BME280
```

---

## Debug UART — Not Wired On This Device

**No debug UART exists on hiking-monitor** — unlike `components/air-quality-monitor/wiring.md`'s Debug UART section (external USB-TTL adapter on GPIO17/UART2), this device has no equivalent tap wired anywhere. Confirmed 2026-09-17, after CARD-0226 (a real reboot-loop investigation) repeatedly assumed otherwise across several dated notes before this was caught.

**Why, concretely:** GPIO17 — the exact pin air-quality-monitor's debug UART TX uses (`hardware_uart: UART2`) — is already committed on this board to the E-ink display's **DC** line (see GPIO Assignment Summary above). There was never a spare pin set aside for this the way air-quality-monitor's build deliberately reserved one.

**Practical consequence:** catching a live serial trace on this specific, already-assembled, field-proven unit isn't a "just run the existing setup" task — it requires either reassigning a GPIO and reflashing (real risk on a unit with no current headroom, not evaluated), or waiting for CARD-0259 (hiking-monitor v2, built on air-quality-monitor's proven architecture — debug UART included by design from the start). See CARD-0226's own 2026-09-17 correction for the investigation this affects.

---

## Schematic Overview

```
┌──────────────────┐                     ┌──────────────────────────────────┐
│  TP4056 + boost  │                     │    ESP32 DevKitC-32 (38-pin)     │
│   (● = pin 1)    │                     │                                  │
│                  │                     │                                  │
│ ●p1 IN+  (grn)   ├──R3(68kΩ)──┬────────┤ GPIO32                           │
│                  │         R4(100kΩ)   │                                  │
│                  │             │       │                                  │
│                  │            GND      │                                  │
│                  │                     │                                  │
│  p2 BAT+ (wht)   ├──R1(100kΩ)──┬───────┤ GPIO35                           │
│                  │         R2(100kΩ)   │                                  │
│                  │             │       │                                  │
│                  │            GND      │                                  │
│                  │                     │                                  │
│  p3 VOUT− (blk)  ├─────────────────────┤ GND               GPIO4 ─────────┼─ BUSY (e-ink)
│  p4 VOUT+ (red)  ├─────────────────────┤ VIN (pin 19)      GPIO5 ─────────┼─ CS   (e-ink)
└──────────────────┘                     │                   GPIO16 ────────┼─ RST  (e-ink)
                                         │                   GPIO17 ────────┼─ DC   (e-ink)
                                         │                   GPIO18 ────────┼─ CLK  (e-ink)
                                         │                   GPIO23 ────────┼─ DIN  (e-ink)
                                         │                                  │
                                         │ GPIO27 ◄(brn) switch (blk)─ GND  │
                                         │ GPIO21 (SDA) ◄─ BME280 + LTR-390 │
                                         │ GPIO22 (SCL) ◄─ BME280 + LTR-390 │
                                         └──────────────────────────────────┘
```
