joscthomas/jctsh/components/hiking-sensor/hiking-sensor-claude-code-instructions.md

# JCTsh Hiking Sensor — Claude Code Instructions
**Author:** Joseph C Thomas (JCT)
**Purpose:** Step-by-step build instructions for the hiking-sensor (hiking-monitor) component.
**Project:** JCT Smart Home (JCTsh)
**Version:** 1.2
**Version description:** Added Steps 23–26: Hiking observations pipeline via Tasker — voice observations captured on the Pixel during hikes, posted directly to the Apps Script doPost endpoint, written to the Hiking Observations sheet with automatic category classification.
**Related files:** JCTsh-hiking-sensor-phase1.md, core/data-pipeline/JCTsh-Environmental-Data-Architecture.md, JCTsh-Build-Standards.md, CLAUDE.md, components/front-porch-temp-sensor/

---

## Overview

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

MQTT component name: `hiking-monitor`

---

## Working Pattern

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

---

## Pre-Flight: Known Issues

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

**2. LTR-390 UV sensor not confirmed in parts inventory.** The inventory update log from 2026-05-28 notes "hiking-sensor, Stock: E-ink display and push buttons added, various other." The LTR-390 is not listed explicitly in the Sensors table. Confirm receipt before Step 3. See Step 1.

---

## Hardware Context

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

**GPIO Assignments:**

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

---

## Network / Integration Architecture

```
BME280 (I2C 0x76) ──┐
LTR-390 (I2C 0x53) ─┤── ESP32 DevKitC-32 (ESPHome + hiking_logger.h)
E-ink display (SPI) ─┤
Button (GPIO32) ─────┤
Battery ADC (GPIO35)─┘
        │
        │ Two operating modes:
        │
        ├── FIELD MODE (no WiFi)
        │       Every 2 min: read sensors → format JSON → write to onboard flash
        │       Button press: update display immediately
        │
        └── HOME MODE (WiFi + MQTT connected)
                On MQTT connect: replay onboard flash log → MQTT data topic
                Every 5 min: publish heartbeat
                Every 2 min: publish live readings directly to MQTT

MQTT broker (Mosquitto, raspberrypi.local:1883)
        │
        ├── jctsh/components/hiking-monitor/data    ← sensor readings + replayed hike logs
        ├── jctsh/components/hiking-monitor/log     ← diagnostic messages
        └── jctsh/components/hiking-monitor/heartbeat ← 5-min heartbeat (home mode only)
                │
                ▼
        Node-RED (wildcard handler: jctsh/components/+/data)
                │ Computes: dew_point_f, heat_index_f
                │ Posts to Google Apps Script → Google Sheets "Environmental Data"
                └── Routes /log → Python log server
                └── Monitors /heartbeat (watchdog wildcard)

Google Sheets ("JCTsh Environmental Data")
        └── Environmental Data sheet (one row per reading, all sources)
```

**MQTT Topics:**

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

**Standard MQTT Payload (from JCTsh-Environmental-Data-Architecture.md):**
```json
{
  "component": "hiking-monitor",
  "ts": "2026-05-27T14:32:00Z",
  "lat": null,
  "lon": null,
  "temp_f": 87.4,
  "humidity_pct": 32.1,
  "pressure_hpa": 1005.2,
  "uv_index": 9.2,
  "battery_v": 3.94,
  "rssi_dbm": -67
}
```
Notes: `lat`/`lon` are always JSON null. `rssi_dbm` is 0 for field-mode readings (no WiFi at time of logging); actual RSSI for home-mode live readings. Derived fields (`dew_point_f`, `heat_index_f`) are computed by Node-RED, not sent by device.

**Log message format:**
```json
{ "component": "hiking-monitor", "category": "System", "message": "..." }
```
Valid categories: `MQTT`, `System`, `Sensor`, `Alert`, `Test`

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

**Display layout:**
```
Temp: 87°F    Humidity: 32%
UV:   9.2     Pressure: ↓
```
Pressure trend arrow: ↑ rising (>+0.5 hPa over last 30 min), ↓ falling (<−0.5 hPa), → steady.

**SmartThings:** Not used. No SmartThings integration.
**HA:** Not used. No HA entities. No MQTT discovery.

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

---

## BENCH PHASE

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

---

## Step 1 — Parts Inventory Confirmation

**STATUS: COMPLETE (2026-06-02)**

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

---

## Step 2 — Create Dedicated MQTT Account

**STATUS: COMPLETE (2026-06-02)**

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

---

## Step 3 — ESPHome Configuration and Wiring Documents

**STATUS: COMPLETE (2026-06-02)**

Files created:
- `hiking-sensor.yaml` — ESPHome config (BME280, LTR-390, e-ink display, button, battery ADC, onboard flash replay, heartbeat)
- `secrets.yaml` — populated with all credentials (gitignored)
- `secrets.yaml.template` — template for reference
- `wiring.md` — complete breadboard wiring reference with STEMMA QT header note for LTR-390
- `hiking_logger.h` — C++ onboard flash logging component
- `ESP32pins.png` — copied from garage-radar

**STATUS: COMPLETE (2026-06-02)**

LTR-390 header pins soldered, files reviewed, ready to wire.

---

## Step 4 — Breadboard Wiring

**STATUS: COMPLETE (2026-06-03)** — all connections wired except battery charger module (deferred to Step 8).

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

**Joseph confirms:** Wiring complete. No shorts. Ready to flash.

---

## Step 5 — Flash Base Firmware and Validate Sensors + Display

**STATUS: COMPLETE (2026-06-03)**

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

---

## Step 6 — Custom Onboard Flash Logging Component Integration

**STATUS: COMPLETE (2026-06-03)**

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

---

## Step 7 — Pressure Trend Validation

**STATUS: COMPLETE (2026-06-03)**

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

---

## Step 8 — Power System Integration

**STATUS: COMPLETE (2026-06-04)**

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

---

## Step 9 — Data Pipeline: Google Sheets Setup

**Claude Code does:** ✓ COMPLETE — `components/hiking-sensor/data-pipeline.md` created. Covers Steps 9–11: Google Sheets setup, Apps Script code and deployment, and Node-RED flow JSON.

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

**Joseph confirms:** Spreadsheet created, both sheets added, spreadsheet ID noted.

---

## Step 10 — Data Pipeline: Google Apps Script Web App

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

---

## Step 11 — Data Pipeline: Node-RED Handler Flow

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

Dew point formula (Magnus approximation):
```
a = 17.27, b = 237.7
gamma = (a * temp_c / (b + temp_c)) + ln(humidity/100)
dew_point_c = (b * gamma) / (a - gamma)
dew_point_f = dew_point_c * 9/5 + 32
```

Heat index formula (NWS Rothfusz regression, valid for temp ≥ 80°F, humidity ≥ 40%):
```
HI = -42.379 + 2.04901523*T + 10.14333127*H - 0.22475541*T*H - 0.00683783*T² 
     - 0.05481717*H² + 0.00122874*T²*H + 0.00085282*T*H² - 0.00000199*T²*H²
```
Where T = temp_f, H = humidity_pct. Use simple formula (T + H/5 - 10.3) when temp < 80°F.

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

---

## Step 12 — Full End-to-End Test

**Claude Code does:** Create `components/hiking-sensor/testing.md` with the complete validation procedure.

**Joseph does:** Run the full end-to-end test:

1. **Sensor validation** — all four sensor values (temp, humidity, pressure, UV) updating every 2 minutes in MQTT Explorer
2. **Display validation** — all four fields rendering correctly on e-ink display; pressure arrow showing "→" (steady)
3. **Button validation** — button press triggers immediate display refresh
4. **Log dashboard** — log messages visible at `http://raspberrypi.local/` under `hiking-monitor`
5. **Heartbeat** — heartbeat appearing every 5 minutes in log dashboard
6. **Field mode simulation:**
   - Change WiFi password in secrets.yaml to wrong value, OTA flash
   - Let device log 5+ readings (10+ minutes)
   - Change password back to correct value, OTA flash
   - Confirm replay: log dashboard shows "Replaying N readings" and "Replay complete"
   - Confirm replayed rows appear in Google Sheets with original timestamps (not current time)
7. **Google Sheets validation:**
   - Confirm Environmental Data sheet has rows from test
   - Confirm `source` column = `hiking-monitor`
   - Confirm `dew_point_f` and `heat_index_f` are populated (not blank)
   - Confirm `lat` = null, `lon` = null
8. **Battery validation:**
   - Confirm `battery_v` column in Sheets shows plausible value (3.7–4.2V)
9. **Power cycle test:**
   - Power off by disconnecting LiPo
   - Power on, confirm device reconnects and resumes normal operation
   - Confirm onboard flash log survives power cycle (if data was logged before power-off, it replays after power-on + WiFi connect)

**Joseph confirms:** Report results for each test item. Identify any failures.

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

---

## Step 13 — Parts Inventory Update

**STATUS: COMPLETE (2026-06-04)**

**Claude Code does:** Update `jctsh-parts-inventory.md` Inventory Update Log:
- ESP32 ×1 used (hiking-sensor)
- BME280 ×1 used (hiking-sensor)
- LTR-390 ×1 used (hiking-sensor)
- E-ink display ×1 used (hiking-sensor)
- Push button ×1 used (hiking-sensor)
- EEMB LiPo ×1 used (hiking-sensor)
- TP4056+boost module ×1 used (hiking-sensor)

Also update the LTR-390 Sensors table entry when confirmed received.

**Joseph confirms:** Inventory updated accurately.

---

## Bench Phase Complete — Install Phase Begins

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

Do not proceed to Install Phase until all bench steps are confirmed complete.

---

## INSTALL PHASE

The hiking sensor install phase is primarily a physical enclosure build, not a location-specific installation like wall-mounted sensors. The device does not have a fixed installed location — it is portable.

---

## Step 14 — Perfboard Build

**Claude Code does:** Create `components/hiking-sensor/perfboard-layout.md` — COMPLETE (2026-06-04)

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

**Joseph does:** Transfer to perfboard per perfboard-layout.md. Validate all sensors reading correctly after transfer.

**Joseph confirms:** Perfboard build complete, all sensors reading correctly, power system functioning.

---

## Step 15 — Enclosure Design

**Claude Code does:** Research and document enclosure design options in `components/hiking-sensor/enclosure.md`:
- Target footprint: ~75mm × 45mm × 20mm
- Requirements: Stevenson-screen louvered port for BME280, LTR-390 on top face, micro USB external, JST external, USB-C internal, button on side, carabiner bail/loop, light-colored PETG
- Evaluate: design from scratch vs. adapt existing open-source Stevenson screen STL

Research questions for enclosure.md:
1. Are there open-source STL files for similar hiking sensor enclosures with Stevenson-screen ventilation?
2. What is the UV transmission rating of natural PETG? (LTR-390 may need a UV-transparent window if recessed — or can be flush-mounted on the top face)
3. What free/low-cost 3D modeling tool is recommended for a first-time enclosure design (if designing from scratch)?

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

**Joseph confirms:** Enclosure approach decided. Report chosen approach.

**Claude Code does:** Update enclosure.md with the decided approach and any specific design guidance needed.

---

## Step 16 — Enclosure Assembly and Final Test

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

**Joseph confirms:** Device assembled. All sensors, display, button, and power system confirmed functional after enclosure assembly.

---

## Step 17 — Field Test

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

---

## Step 18 — README and Final Housekeeping

**Claude Code does:** Create `components/hiking-sensor/README.md` following the garage-radar README pattern. Must include:
- What the component does (field mode + home mode)
- Hardware table
- GPIO assignment table
- Wiring overview
- MQTT topics (data, log, heartbeat)
- Operating modes: field vs. home
- Onboard flash logging: file name, format, capacity
- Replay behavior: trigger, throttle, log messages
- Power system: TP4056+boost, LiPo, voltage divider
- Display: layout, update interval, button behavior
- Data pipeline: Google Sheets, Apps Script, Node-RED flow
- Known behaviors / tuning notes
- Deferred future enhancements
- Build document index

Also do the following final housekeeping:
1. Add `hiking-monitor` to root `README.md` Components list
2. Add `hiking-monitor` to root `CLAUDE.md` credentials table (MQTT account)
3. Add hiking-monitor IP, hostname `hiking-monitor.local`, and MAC to `jctsh-network.md` (obtain IP and MAC from ESPHome logs or router DHCP table)
4. Update `JCTsh-Parts-Inventory.md` inventory update log (Step 13 above)

**Joseph confirms:** README complete and accurate. All housekeeping items done.

---

## Backlog

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

---

## Future Enhancements

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

---

## Notes for Claude Code

- **Flash path:** Always flash from `C:\esphome\hiking-sensor\` — not from the repo path. Spaces in "JCT Documents" break the ESP-IDF compiler. Copy YAML, secrets.yaml, and hiking_logger.h to that directory before every flash.
- **ESPHome MQTT discovery:** Set `discovery: false` — the hiking monitor is not integrated with Home Assistant. No HA entities needed.
- **E-ink display model string:** The Waveshare 2.13" V4 SSD1680 likely uses model `2.13in-ttgo-b74` in ESPHome `waveshare_epaper` platform. Confirm at Step 5 — try `2.13in-ttgo-b74` first; if display shows garbage or doesn't initialize, try `2.13in-b74` or check current ESPHome docs for SSD1680 model strings.
- **Unicode arrows on e-ink:** ESPHome `waveshare_epaper` rendering uses bitmap fonts. Unicode arrows (↑ → ↓) require the font to include those glyphs. If rendering fails, fall back to ASCII: `^` / `=` / `v`. Confirm in Step 7.
- **ESP32 filesystem in ESPHome/Arduino:** Use SPIFFS via the ESP-IDF native VFS (`esp_spiffs.h`) — bundled with ESP-IDF, no external library needed. LittleFS (`LittleFS.h`, Arduino ESP32 core) is the alternative with better wear-leveling and directory support, but neither advantage matters for a single-file sequential log. Reference implementation: `hiking_logger.h`.
- **MQTT account:** Create before first flash. Account name: `hiking-monitor`. Commands: see mqtt-account-setup.md. Ownership gotcha: `mosquitto_passwd` resets file group to root — always run `sudo chown root:mosquitto /etc/mosquitto/passwd` immediately after.
- **Heartbeat:** Only publish heartbeat when WiFi + MQTT connected. Guard the heartbeat interval with a `wifi.connected` condition. Do not publish heartbeats during field mode — they would pile up and replay incorrectly.
- **rssi_dbm in field mode:** When logging to onboard flash in field mode (no WiFi), set `rssi_dbm` to `0` in the payload. Node-RED or Sheets analysis can filter `rssi_dbm = 0` to identify field-mode readings. Do not read wifi_signal sensor when WiFi is not connected — it returns NaN.
- **Pressure trend calculation:** Store a circular buffer of 16 pressure readings. Compare current reading to the reading 15 cycles ago (15 × 2 min = 30 min). Initialize all buffer slots to 0; guard against comparing to uninitialized slots (value == 0 means no history yet).
- **Node-RED flow:** The wildcard `jctsh/components/+/data` handler is new infrastructure — it does not exist yet. Build it in Step 11. The existing `jctsh/+/+/log` and `jctsh/+/+/heartbeat` wildcard handlers already exist and catch the hiking monitor automatically.
- **Apps Script auth:** The secret key in the URL query parameter is sufficient for this use case. No OAuth needed. URL format: `https://script.google.com/macros/s/<ID>/exec?key=<SECRET>`. Node-RED uses env vars for both.
- **Network entry:** After first successful boot, retrieve hiking-monitor IP and MAC from the ESPHome log or router DHCP table. Add to jctsh-network.md. Reserve the DHCP IP on the router.
- **Bench-first rule:** Steps 14–18 (enclosure, field test) come after all bench steps are confirmed. Do not skip to enclosure before the full end-to-end test (Step 12) passes.
- **Build Standards reference:** JCTsh-Build-Standards.md appears to have incorrect content (parts inventory instead of build standards). Standards are derived from existing component patterns (front-porch-temp-sensor, garage-radar) throughout these instructions. Joseph should investigate and restore the correct file.

---

## ITERATIVE REFINEMENT PHASE

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

---

## Step 19 — GPSLogger Configuration and Google Sheets GPS Track

**Claude Code does:** Create `components/hiking-sensor/gps-pipeline.md` documenting the full GPS correlation architecture:

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

---

## Step 20 — Node-RED lat/lon Population in Wildcard Data Handler

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

---

## Step 21 — Pixel Hotspot Second WiFi Network

**Claude Code does:** Update `hiking-sensor.yaml` to add the Pixel hotspot as a second WiFi network. Update `wiring.md` (or create a `wifi-config.md` note if wiring.md is not the right home) to document the two-network configuration.

ESPHome `wifi:` block change:
```yaml
wifi:
  networks:
    - ssid: !secret wifi_ssid
      password: !secret wifi_password
    - ssid: !secret hotspot_ssid
      password: !secret hotspot_password
  ap:
    ssid: "hiking-monitor-fallback"
    password: !secret ap_password
```

Add to `secrets.yaml`:
```yaml
hotspot_ssid: "<Pixel hotspot SSID>"
hotspot_password: "<Pixel hotspot password>"
```

Add to `secrets.yaml.template`:
```yaml
hotspot_ssid: "<Pixel hotspot SSID>"
hotspot_password: "<Pixel hotspot password>"
```

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

**Joseph does:**
1. Set a fixed Pixel hotspot SSID and password on the Pixel 10 Pro XL (note: changing these later requires re-flashing the device)
2. Add hotspot credentials to `secrets.yaml`
3. OTA flash updated YAML from `C:\esphome\hiking-sensor\`
4. With home WiFi unavailable (or temporarily disabled on the device), enable Pixel hotspot
5. Confirm device connects to hotspot
6. Confirm device connects to home Mosquitto broker over cellular
7. With a few readings in onboard flash (log a short field mode session first), confirm replay occurs over hotspot connection
8. Confirm replayed readings appear in Google Sheets with correct timestamps

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

---

## Step 22 — Harvest New Patterns into Build Standards

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

Do not write changes to `JCTsh-Build-Standards.md` until Joseph reviews and approves.

**Joseph does:** Review proposed additions. Approve, modify, or reject each one.

**Joseph confirms:** Approved additions identified. Proceed to update `JCTsh-Build-Standards.md`.

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

---

## Step 23 — Hiking Observations: Update Apps Script

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

The deployment URL does not change.

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

```powershell
$url = "https://script.google.com/macros/s/<SCRIPT_ID>/exec?key=<KEY>"
$body = '{"component":"hiking-observations","ts":"2026-06-13T17:00:00Z","lat":null,"lon":null,"observation":"saw a hawk circling above the ridge, very clear sky today","categories":[],"source":"voice"}'
Invoke-RestMethod -Uri $url -Method Post -ContentType "application/json" -Body $body
```

Expected response: `{"status":"ok"}`

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

**Joseph confirms:** Row in sheet is correct. Proceed to Step 24.

---

## Step 24 — Hiking Observations: Create Tasker Task

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

1. Open Tasker → Tasks tab → **+** → name it `Log Observation`

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

5. **Action 4 — Notify:**
   - Search for **Flash**
   - Text: `Observation logged`

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

**Joseph confirms:** Manual task test produced a correct row in the sheet. Proceed to Step 25.

---

## Step 25 — Hiking Observations: Home Screen Widget

**Joseph does:** Add the Tasker task as a one-tap home screen widget on the Pixel:

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

**Joseph confirms:** Widget tapped, observation spoken, row appeared in sheet. Proceed to Step 26.

---

## Step 26 — Hiking Observations: End-to-End Field Simulation

**Joseph does:** Simulate a hiking observation session:

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

**Joseph confirms:** Both rows correct. CARD-0007 is done — move to Done in backlog.
