joscthomas/jctsh/tos/JCTsh-Operating-System-History.md

# JCTsh-Operating-System.md — Version History

Full changelog for `JCTsh-Operating-System.md`, split out (CARD-0292) once the live
document's own "Version description" header field had grown into a ~6KB chain of
"Prior version description" entries — over 20% of the file's own size. Read on demand
only, not part of routine reading. The live document's header now states only the
current version and its own description.

**Note on completeness:** versions 1.13 down to 1.6 map cleanly one entry per version
(the chaining convention was used consistently from 1.6 onward). Versions 1.2–1.5 were
never individually chained — each of those four edits fully restated the field rather
than prefixing a "Prior version description," so their descriptions survived only
bundled together into one paragraph, reconstructed as best as possible below. Version
1.1's original description ("Added a Priority section...") and 1.0's are not recoverable
from the current file at all — they were overwritten before the chaining convention
began.

---

| Version | Description |
|---|---|
| 1.23 | Added a never-print-a-credential rule to Engineering Discipline, 2026-10-02 (CARD-0334 Phase 4). The rule already existed in CARD-0334's own text and in root `CLAUDE.md`'s Credentials section, but was never stated in this document, where every other cross-cutting discipline rule (additive-first, verify-before-trusting, iterative/incremental) lives -- the exact "discover an implied convention and give it a real home" gap the Engineering Discipline section's own closing bullet describes. Also corrected `CLAUDE.md`'s "credentials are kept off-disk" line, which was never accurate -- most live in plaintext, gitignored files (`credentials.local.md`, `secrets.yaml`/`secrets.h`, `.env` files), not off-disk; `CLAUDE.md` now also points at `tos/credential-registry.yaml` (the values-free inventory) and the in-progress M8-hosted vault (CARD-0372). |
| 1.22 | Dropped Design as a board column/Status value (Joseph, 2026-09-28) — found live via CARD-0349: `kanban-board.md`'s own header and the live `/kanban` dashboard's parser (`core/logging/log_server.py`'s `_KANBAN_COLUMNS`) had only ever recognized Backlog/Planning/Build/Done/Defer, so a card with `Status: Design` (this document's own stated column set) was silently invisible on `/kanban` — parsed by the file's own rules but not this document's. Rather than reconciling the other direction (adding Design back to the header/parser), Joseph decided to retire it here instead, since it was already barely used in practice (the "Observed Exception: Skipping Design" section, now removed, existed specifically because most cards already skipped straight from Planning to Build). Board Columns table, State Transitions table (Planning → Design and Design → Build collapsed into one Planning → Build row), the "Note on Planning" cross-reference, and the "Applying TOS to Pre-Existing Work" example wording all updated to match; the Observed Exception section itself removed outright (it described skipping a column that no longer exists, not a superseded claim worth striking through in place). |
| 1.21 | CARD-0325 — Board Commit Rule: commit `tos/kanban-board.md` on completion, never ask, never wait; lock file rejected (struck in place), hunk-level board staging ruled mechanically unavailable, attribution drift accepted and deliberately not instrumented. Adds the Card ID allocation rule (allocate late from the file, push serializes, later pusher renumbers) and a mid-day protocol-propagation step (notify live peer sessions via SendMessage; a running session never re-reads this document). |
| 1.20 | CARD-0303 — moved "Concurrent Sessions" here from root `CLAUDE.md` (pure process/policy, previously homeless); added two more principles found live during this same reconciliation — "merge, don't just delete" as a corollary to single-source-of-truth, and "superseding stale content: mark and strike through, don't silently delete" (from `JCTsh-Build-Standards.md` §5's own internal contradiction with §6.4, found and fixed the same pass). |
| 1.19 | CARD-0304 follow-on, same session — two more principles added (single source of truth/eliminate redundancy in Documentation Structure, iterative-and-incremental in Engineering Discipline) after discovering they'd been confirmed correct in conversation but never actually landed in v1.18, despite that version's own commit claiming "ten principle gaps found and filled." Caught by applying v1.18's own new "verify a claimed completion directly" rule to v1.18 itself. |
| 1.18 | CARD-0304 — ten principle gaps found and filled: reworded Where Work Happens (pre-card thinking isn't tool-specific); added the plan/as-built/card distinction under Note on Build (the plan is never retroactively cleaned up); added interview-first and explicit-non-goals to Core Principle; named the explicit-decisions-never-silent-defaults thread connecting four existing rules; added verify-a-claimed-completion, measured-thresholds, and the discover-and-document-implied-conventions meta-principle to Engineering Discipline; added live-verification-beats-synthetic to Note on Build; and stated the README-vs-CLAUDE.md content split explicitly in Documentation Structure for the first time (previously only in root CLAUDE.md, now trimmed to a pointer there). |
| 1.17 | Expanded Relationship to Commit / Push with the full commit/push-without-asking conditions (previously only in the unversioned, repo-external global CLAUDE.md) — Joseph: keeping it there "obscures the existence of the rule" compared to a discoverable tos/ file. Global preferences trimmed to a cross-project pointer. |
| 1.16 | Added a "Retracting a card" note to State Transitions (CARD-0302) — formalizes an observed-but-undocumented convention (distinct from Defer: the card itself shouldn't have existed, almost always a duplicate found after the fact) already used three times (CARD-0252, CARD-0253, CARD-0302 itself) with no written definition until now. |
| 1.15 | Added a Documentation Structure rule for a document's own version-tracking (CARD-0292) — split into a sibling `<Doc>-History.md` once it stops being a short header field, with a concrete trigger (a real "Prior version description" chain or dedicated table). Applied immediately to this document, `JCTsh-Component-Session-Start.md`, and `JCTsh-Build-Standards.md`. |
| 1.14 | Split this "Version description" chain out of `JCTsh-Operating-System.md` into this file (CARD-0292) — it had grown to ~6KB, over 20% of the file. From this version on, the live document's header holds only the current version's description; this file is the complete record. |
| 1.13 | Corrected the Component/Cluster Sessions section's framing (CARD-0284 follow-on, Joseph) — a component/cluster session runs a *modified* general Session Start (per-step scoped/skipped/unscoped, see `JCTsh-Component-Session-Start.md`'s table), not the general steps unmodified plus extras as previously stated. |
| 1.12 | Extended the Listing open cards convention (CARD-0288 follow-on, Joseph) — a requested open-cards listing is always a table (ID/Status/Title), ordered by Priority tier first, then by Session Card Selection's four factors within each tier; the two ordering concepts previously had no stated interaction. |
| 1.11 | Added two Documentation Structure notes (CARD-0290, Joseph) — (1) archived card history now gets its own `card-archive.md` per component, never appended into `CLAUDE.md` directly (the same working-file/archive split `kanban-board.md`/`kanban-archive.md` already has, applied at the component-doc layer after `components/hike-izer/CLAUDE.md` reached 485KB); (2) a component-doc filename standard — unprefixed by default (matches `README.md`/`CLAUDE.md`'s own locked, unprefixed names), prefixed only when a file is commonly referenced by name outside its own directory context. Explicitly a process/documentation rule, not a technology one — corrected after initially proposing it for `JCTsh-Build-Standards.md`, which doesn't fit a rule that applies the same regardless of a component's hardware. |
| 1.10 | Added a Component/Cluster Sessions section pointing to the new `JCTsh-Component-Session-Start.md` (CARD-0284, Joseph) — a session with a standing, resumed identity for a specific component or cluster (distinct from a general session with no such persistent focus) runs extended startup steps beyond `CLAUDE.md`'s general Session Start: read each covered component's `README.md` and `CLAUDE.md` fully, and scope the kanban/marker checks to its own component tags specifically, not just rely on the whole-board general sweep. Same session-behavior-document pattern as `JCTsh-Session-Card-Selection.md`. |
| 1.9 | Extended Engineering Discipline's "Investigate existing patterns first" rule to explicitly cover hardware/physical capability claims (CARD-0226/CARD-0222/CARD-0258, Joseph) — check a component's own `README.md`/detail docs before relying on or asserting what it can physically do, never infer from a sibling component's build. Raised directly by a real miss: five dated notes on CARD-0226 assumed hiking-monitor could run air-quality-monitor's debug-UART setup, never checked hiking-monitor's own `wiring.md`, which shows it was never wired for one. Root `CLAUDE.md`'s own pointer corrected to match — `README.md` is the permanent hardware/capability reference per `JCTsh-Build-Standards.md` §7.1, `CLAUDE.md` is history/rationale, and the two were being conflated. |
| 1.8 | Added an Accepted-limitation closure note under Note on Build (CARD-0258, Joseph: "i like it") — a card can reach Done with its root-cause criterion unmet, but only when a built mitigation is confirmed working live, the unmet piece is specifically causal (not functional) understanding, no practical investigative path remains, and a person makes that call explicitly. Distinguished from Defer (no working mitigation at all) and from a card with a still-active lead (doesn't qualify yet, e.g. CARD-0222 pending CARD-0226/CARD-0221's UART-capture path). |
| 1.7 | Added a Listing open cards subsection to Auto Verify / Watch For Markers (CARD-0258, Joseph) — when a session lists open cards for Joseph directly (not the `/kanban` dashboard), cards carrying an active marker are omitted from the visible list entirely (not just sorted last) and rolled up into a single count at the end, mirroring `/kanban`'s existing sort-to-end reasoning that a marker-carrying card doesn't need attention right now. |
| 1.6 | Added an Auto Verify / Watch For Markers section (CARD-0251/CARD-0258) — promotes the ad hoc marker practice CARD-0251 built into a real documented home, per that card's own "promote once proven out" plan. Formalizes a resolution protocol that didn't exist before: found live via CARD-0258, where a Watch for marker was actually resolved but its original marker line was never edited to stop matching the parser's literal-text regex, leaving both the `/kanban` badge and every future Session Start's grep treating an already-answered check as still open indefinitely. |
| 1.2–1.5 | (Bundled — never individually chained.) Added a Session Card Selection pointer (CARD-0288) to the new standalone `JCTsh-Session-Card-Selection.md` — four ordered factors governing which card a session actually picks up next, distinct from the Priority section's urgency tag, applied by default each session. Added a Documentation Structure section (CARD-0289) — split docs by topic/read-frequency, not file count, and keep cross-references current; generalizes `JCTsh-Build-Standards.md` §7.1a's README/CLAUDE.md split into a repo-wide rule. Added a reconciliation note cross-referencing `JCTsh-Build-Standards.md` — this document covers process/policy/workflow, that one covers technology/build conventions; the boundary case (documentation structure) generalizes in whichever doc is broader and cross-references the narrower one. Moved two process rules out of `JCTsh-Build-Standards.md` (CARD-0289 follow-on): §6.1/§6.3 (Additive First, Existing Pattern Investigation) generalized into a new Engineering Discipline section; §7.5 (Documentation Captures Reality) folded into the Note on Build. |
| 1.1 | Added a Priority section — four levels (Critical/High/Medium/Low), independent of column/state, defining how urgently a card needs attention rather than how far along it is. Used whenever prioritization is asked for. |

**Related:** `tos/kanban-board.md` CARD-0292 (this split), `JCTsh-Build-Standards-History.md` (the analogous split for that document), `JCTsh-Component-Session-Start-History.md` (same pattern, that document).
