joscthomas/jctsh/tos/New-Repo-Setup-Protocol.md

# New Repo Setup Protocol

**Author:** Joseph C Thomas (JCT), via Claude
**Purpose:** The repeatable procedure for moving a distinct personal content domain
(currently living as a plain, unversioned folder) into its own dedicated git repo under
`Projects/` — extracted from CARD-0297 (LogSeq) and CARD-0298 (Pastor Ben blog), the two
real instances that established this pattern, so the next one (e.g. CARD-0317, Bible study
content) doesn't rediscover the same lessons from scratch.
**Version:** 1.3
**Version description:** Step 9 now also covers interviewing for and writing this repo's
purpose section in `tos/Repo-Purposes.md` (CARD-0320, 2026-09-20) — folded in there rather
than as a new numbered step, since it's a natural extension of "describe what this repo is,"
just answering "what it's for" instead. Prompted by defining `Rethinking-Scripture-Bible-Study`'s
own purpose retroactively (it was created under v1.2, before this step existed).
**Prior version (1.2):** added step 13, optional `/kanban` dashboard onboarding (CARD-0317,
2026-09-20) — folded into this doc rather than a separate one (Joseph's call): the procedure
is small, jctsh-specific (not part of the new repo itself, hence "optional"), and has now
happened three times in a row as the natural next step after repo creation.
**Prior version (1.1):** added the "Confirmation gates" section and strengthened the
`.gitignore` step, after this protocol's real third execution (CARD-0317) still skipped two
things it already documented (visibility, card-migration confirmation) plus one it hadn't
(`.gitignore` as an explicit decision) — all folded into the same general "yes, build this"
that authorized the whole card.
**Related:** `Protocol-Placement.md` (this doc's own placement — "shared by some projects,"
interim home in jctsh's `tos/`), `Portable-Kanban-Template.md` (used in step 8), CARD-0297,
CARD-0298 (the precedent), CARD-0301 (created `Projects/` itself and the portable template).

---

**Scope:** a distinct content domain — one person's blog, notes system, or similar — that
belongs in its own repo rather than folded into jctsh or another existing one. Not for a new
jctsh component (that's `JCTsh-Component-Session-Start.md`'s territory instead).

**Confirmation gates — these need their own explicit yes, never inferred from a general
"create the repo" go-ahead (added 2026-09-20, CARD-0317's real miss — both of these were
already written into steps 1 and 8 below, and still got skipped in practice: visibility was
assumed private from precedent instead of asked, and CARD-0317's content got moved into the
new repo's board before Joseph confirmed that specific move, not just the repo's creation).
A general "yes, build this" authorizes the mechanical steps; it does not answer these two on
its own:**
1. **Visibility** (step 1) — ask every time, even when every prior instance came back
   "private." A strong pattern is not a decision already made for the next one.
2. **Migrating an originating card's content into the new repo's board** (step 8) — a
   separate ask from "create the repo," not bundled into it.
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
