joscthomas/jctsh/tos/Remote-Control-Setup.md

# Claude Code Remote Control Setup

**Author:** Joseph C Thomas (JCT), via Claude
**Purpose:** How to actually connect the Claude Android app to a Claude Code session running
on this desktop — CARD-0296 raised this after an initial attempt (2026-09-19) opened the
Android app cold and got a brand-new, disconnected cloud session instead of the desktop one.
**Version:** 1.0
**Version description:** Initial version, written 2026-09-20 from `claude-code-guide` agent
research against Claude Code's own docs (code.claude.com/docs/en/remote-control.md).
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
